TNTECHARC/TALUS-legacy/2015 Stuff/3D Printed Parts - 2015/Shoulders/Left Shoulder/leftPivcenterV1.stl

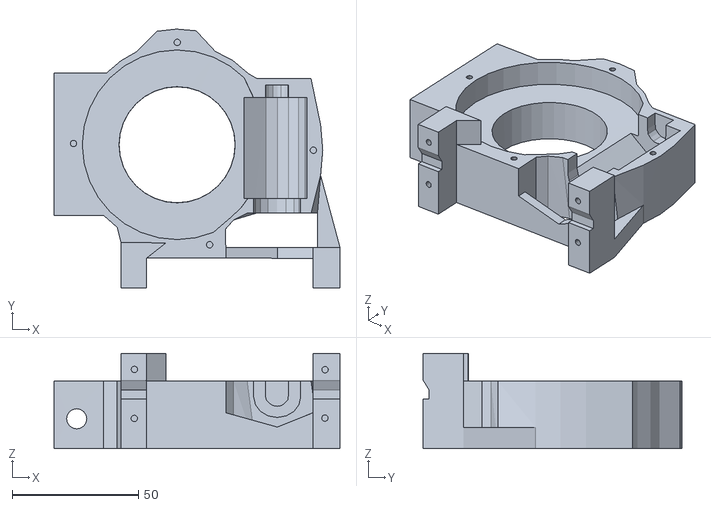
[picture p18: CAD file, 2019-11-21]
2015 Stuff/3D Printed Parts - 2015/Shoulders/Left Shoulder/leftPivcenterV1.stl
113.4 x 102.6 x 37.8
