TNTECHARC/TALUS-legacy/2015 Stuff/3D Printed Parts - 2015/Stomach/StomSupportRightV1.stl

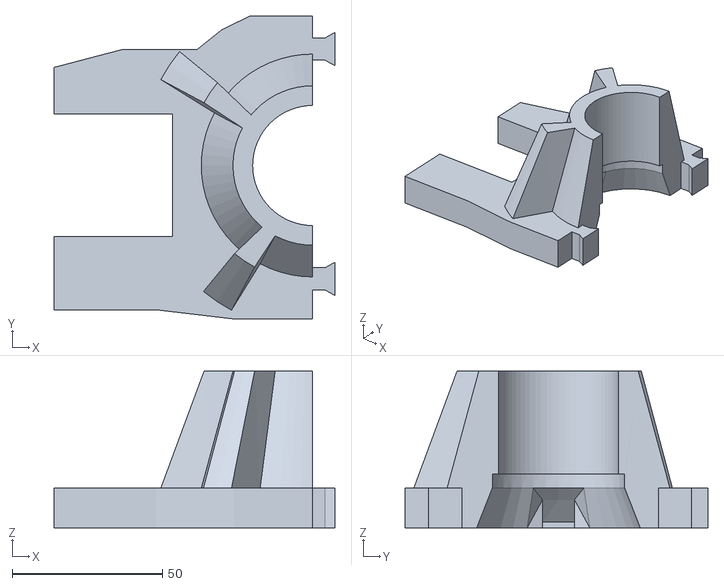
[picture p19: CAD file, 2019-11-21]
2015 Stuff/3D Printed Parts - 2015/Stomach/StomSupportRightV1.stl
93.5 x 101.0 x 52.2
