TNTECHARC/TALUS-legacy/2015 Stuff/F17 ME4140 Animation Project/Matlab Code and Rigid-Body STLS/Right_Forearm.stl

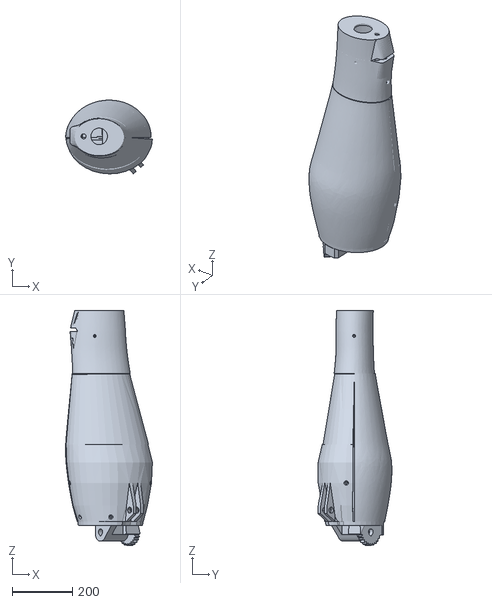
[picture p20: CAD file, 2019-11-21]
2015 Stuff/F17 ME4140 Animation Project/Matlab Code and Rigid-Body STLS/Right_Forearm.stl
287.9 x 244.5 x 779.1
