TNTECHARC/TALUS-legacy/2015 Stuff/3D Printed Parts - 2015/Arms/GearHolderV1.stl

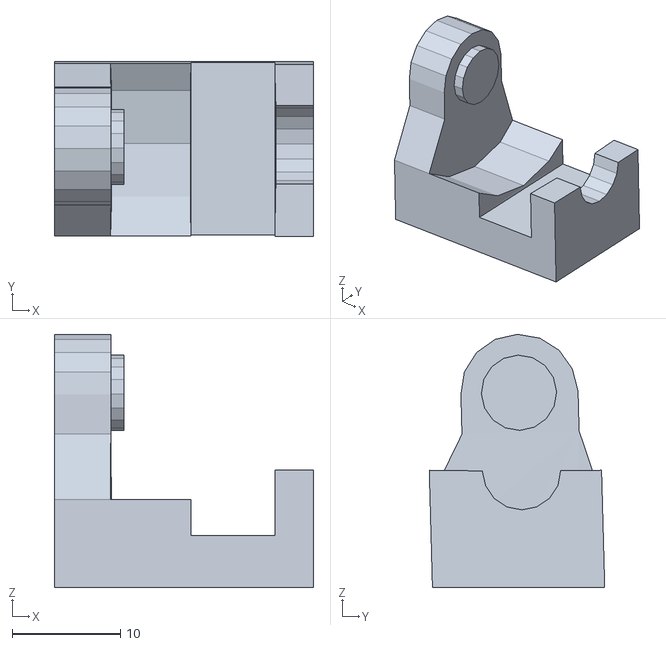
[picture p21: CAD file, 2019-11-21]
2015 Stuff/3D Printed Parts - 2015/Arms/GearHolderV1.stl
23.9 x 16.2 x 23.4
