TNTECHARC/TALUS-legacy/2015 Stuff/3D Printed Parts - 2015/Shoulders/Left Shoulder/PivGearV4.stl

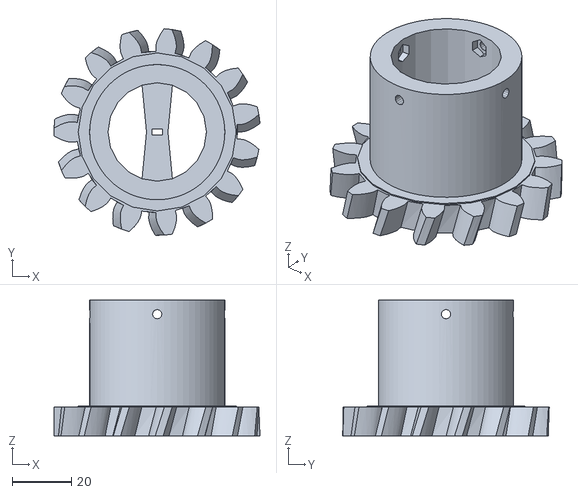
[picture p22: CAD file, 2019-11-21]
2015 Stuff/3D Printed Parts - 2015/Shoulders/Left Shoulder/PivGearV4.stl
69.5 x 69.7 x 45.7
