TNTECHARC/TALUS-legacy/2015 Stuff/3D Printed Parts - 2015/Shoulders/Right Shoulder/PivPotholderV2.stl

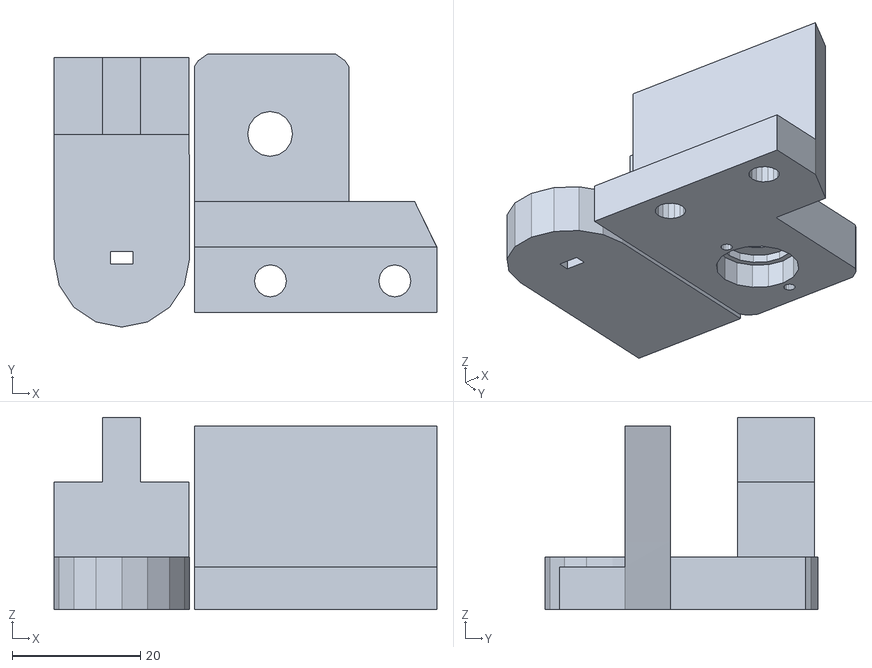
[picture p23: CAD file, 2019-11-21]
2015 Stuff/3D Printed Parts - 2015/Shoulders/Right Shoulder/PivPotholderV2.stl
59.6 x 42.5 x 30.0
