TNTECHARC/TALUS-legacy/2015 Stuff/3D Printed Parts - 2015/Stomach/TStoBackRightV1.stl

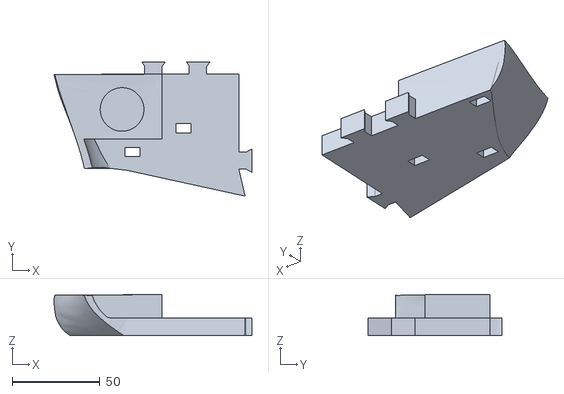
[picture p24: CAD file, 2019-11-21]
2015 Stuff/3D Printed Parts - 2015/Stomach/TStoBackRightV1.stl
112.7 x 76.4 x 23.4
