TNTECHARC/TALUS-legacy/2015 Stuff/3D Printed Parts - 2015/Torso/NeckV1.stl

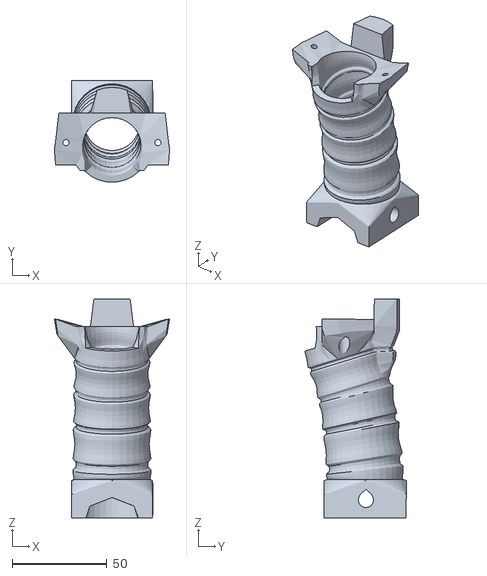
[picture p25: CAD file, 2019-11-21]
2015 Stuff/3D Printed Parts - 2015/Torso/NeckV1.stl
60.7 x 53.5 x 115.4
