TNTECHARC/TALUS-legacy/2015 Stuff/F17 ME4140 Animation Project/Matlab Code and Rigid-Body STLS/Right_Shoulder2.stl

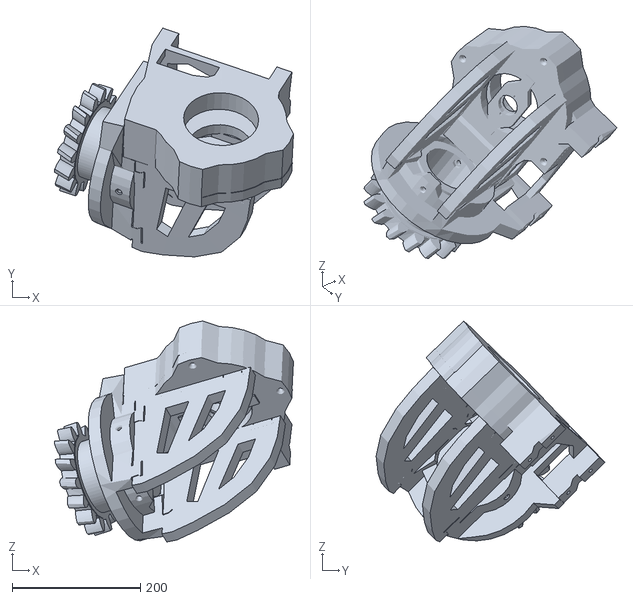
[picture p26: CAD file, 2019-11-21]
2015 Stuff/F17 ME4140 Animation Project/Matlab Code and Rigid-Body STLS/Right_Shoulder2.stl
372.1 x 356.3 x 344.1
