TNTECHARC/TALUS-legacy/2015 Stuff/3D Printed Parts - 2015/Arms/leftRotTitV2.stl

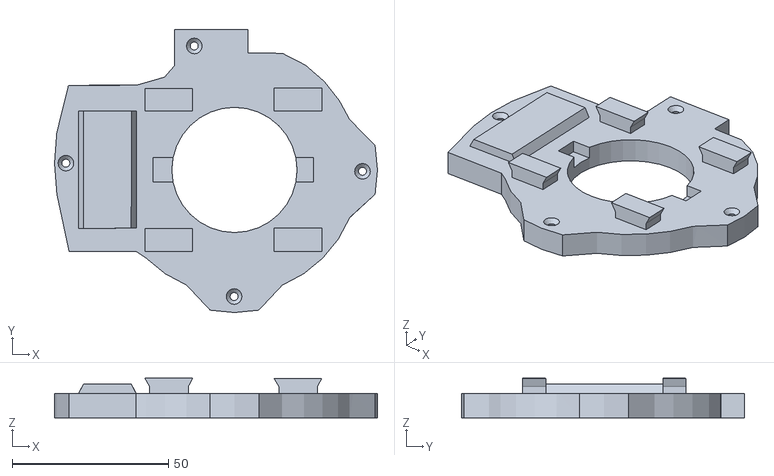
[picture p27: CAD file, 2019-11-21]
2015 Stuff/3D Printed Parts - 2015/Arms/leftRotTitV2.stl
103.5 x 90.7 x 12.7
