TNTECHARC/TALUS-legacy/2015 Stuff/3D Printed Parts - 2015/Shoulders/Left Shoulder/servoholderV1.stl

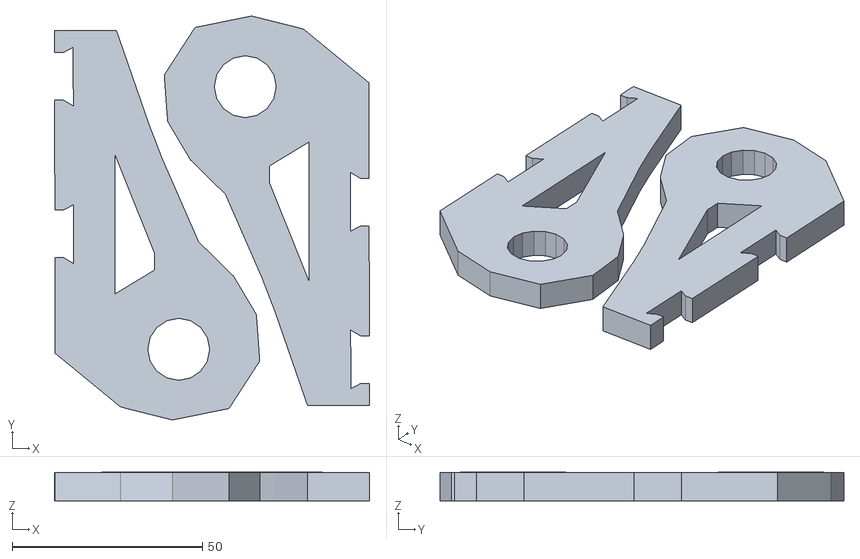
[picture p28: CAD file, 2019-11-21]
2015 Stuff/3D Printed Parts - 2015/Shoulders/Left Shoulder/servoholderV1.stl
82.8 x 106.2 x 7.56
