TNTECHARC/TALUS-legacy/2015 Stuff/3D Printed Parts - 2015/Stomach/TStoFrontLeftV1.stl

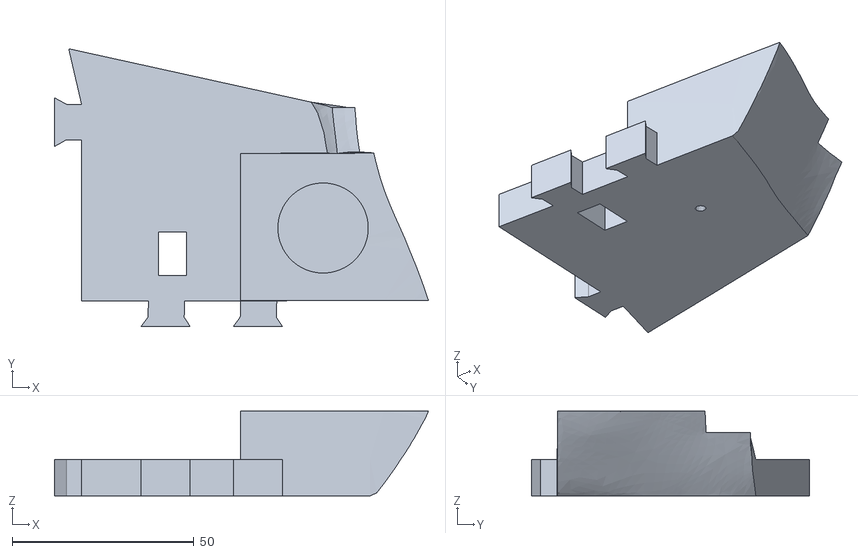
[picture p29: CAD file, 2019-11-21]
2015 Stuff/3D Printed Parts - 2015/Stomach/TStoFrontLeftV1.stl
103.0 x 76.4 x 23.4
