TNTECHARC/TALUS-legacy/2015 Stuff/3D Printed Parts - 2015/Torso/homplateback+V1.stl

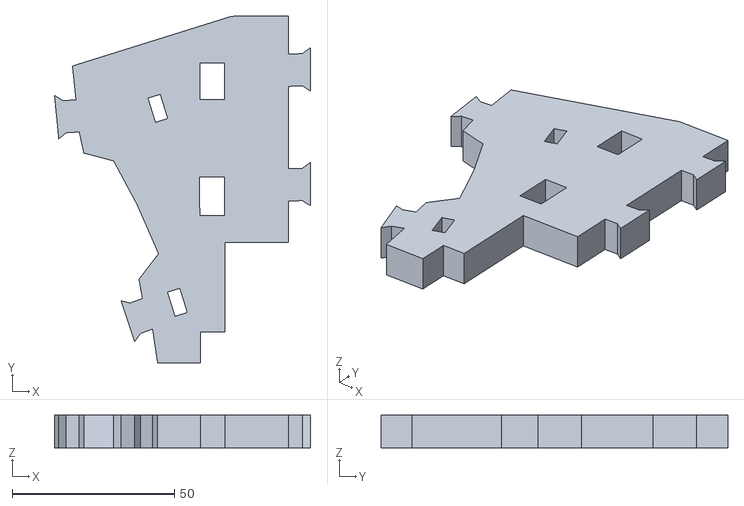
[picture p30: CAD file, 2019-11-21]
2015 Stuff/3D Printed Parts - 2015/Torso/homplateback+V1.stl
79.0 x 107.0 x 10.0
