TNTECHARC/TALUS-legacy/2015 Stuff/3D Printed Parts - 2015/Arms/RotGearV4.stl

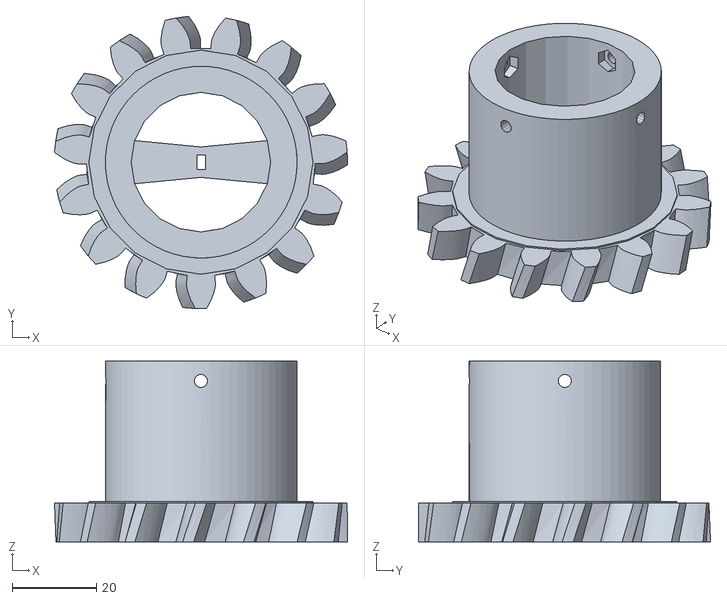
[picture p31: CAD file, 2019-11-21]
2015 Stuff/3D Printed Parts - 2015/Arms/RotGearV4.stl
69.7 x 69.5 x 43.0
