TNTECHARC/TALUS-legacy/2015 Stuff/3D Printed Parts - 2015/Shoulders/Left Shoulder/PivConnectorV1.stl

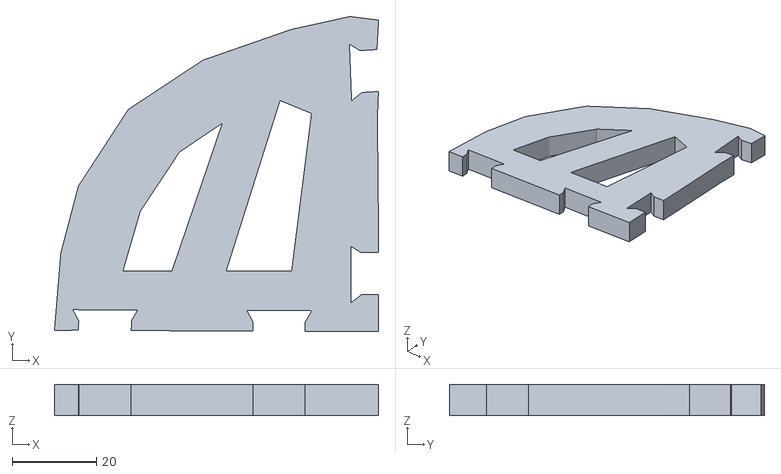
[picture p32: CAD file, 2019-11-21]
2015 Stuff/3D Printed Parts - 2015/Shoulders/Left Shoulder/PivConnectorV1.stl
77.1 x 74.9 x 7.49
