TNTECHARC/TALUS-legacy/2015 Stuff/3D Printed Parts - 2015/Stomach/RollFrontRightV1.stl

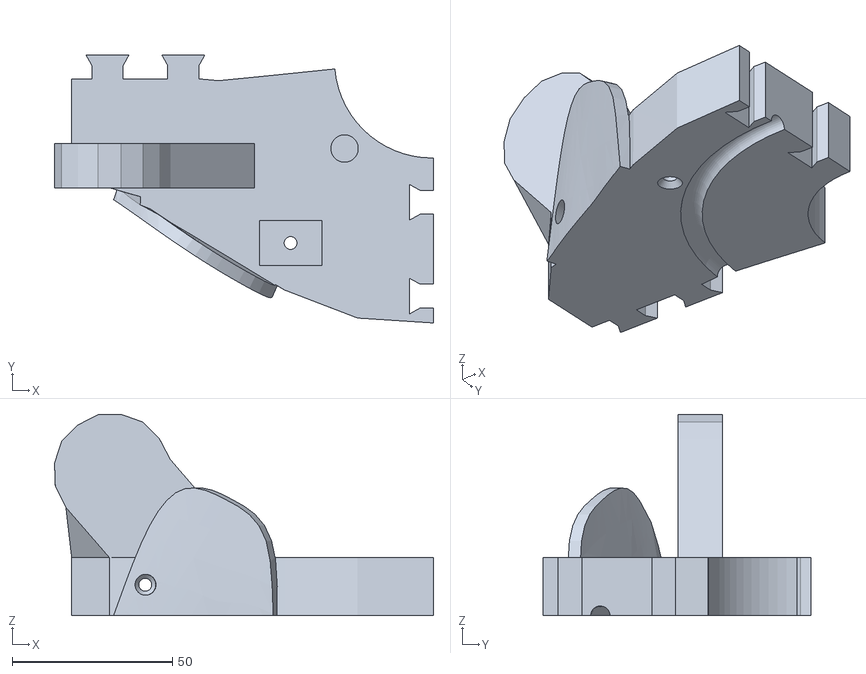
[picture p33: CAD file, 2019-11-21]
2015 Stuff/3D Printed Parts - 2015/Stomach/RollFrontRightV1.stl
118.4 x 83.7 x 62.9
