TNTECHARC/TALUS-legacy/2015 Stuff/3D Printed Parts - 2015/Torso/ThroatHoleV2.stl

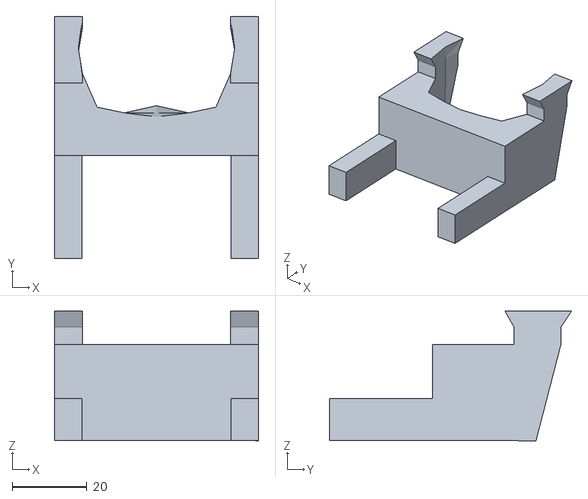
[picture p34: CAD file, 2019-11-21]
2015 Stuff/3D Printed Parts - 2015/Torso/ThroatHoleV2.stl
54.6 x 64.8 x 34.7
