TNTECHARC/TALUS-legacy/2015 Stuff/F17 ME4140 Animation Project/Matlab Code and Rigid-Body STLS/Right_Bicep.stl

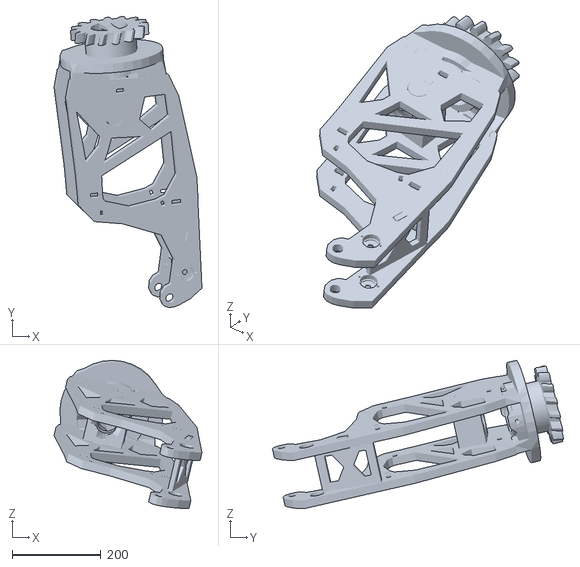
[picture p35: CAD file, 2019-11-21]
2015 Stuff/F17 ME4140 Animation Project/Matlab Code and Rigid-Body STLS/Right_Bicep.stl
334.4 x 657.8 x 335.1
