TNTECHARC/TALUS-legacy/2015 Stuff/3D Printed Parts - 2015/Arms/reinforcerV1.stl

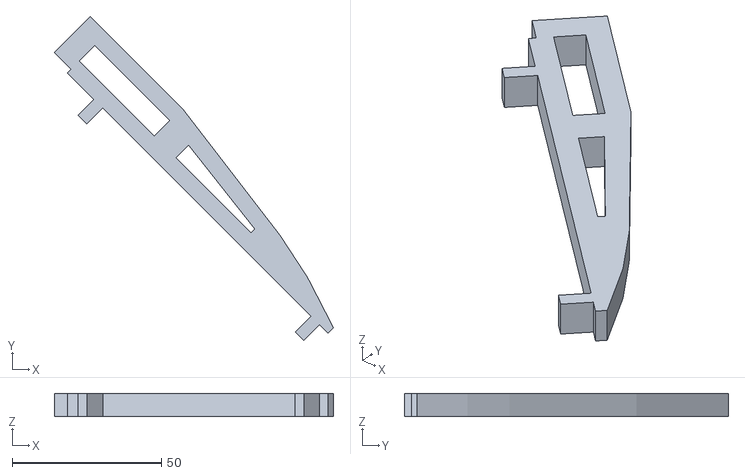
[picture p36: CAD file, 2019-11-21]
2015 Stuff/3D Printed Parts - 2015/Arms/reinforcerV1.stl
93.6 x 108.7 x 7.77
