TNTECHARC/TALUS-legacy/2015 Stuff/3D Printed Parts - 2015/Shoulders/Right Shoulder/PivWormV2.stl

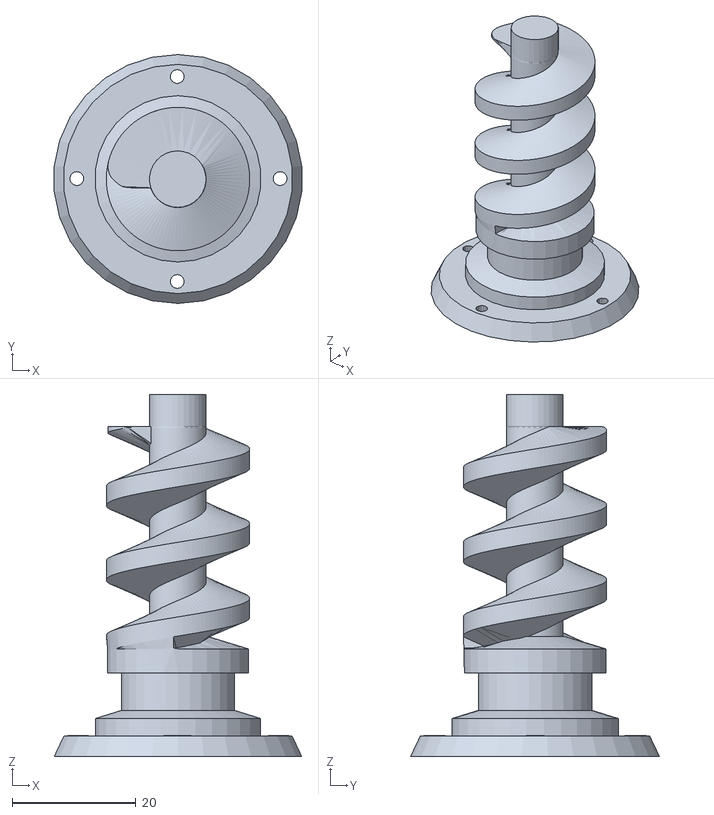
[picture p37: CAD file, 2019-11-21]
2015 Stuff/3D Printed Parts - 2015/Shoulders/Right Shoulder/PivWormV2.stl
39.9 x 40.2 x 58.4
