TNTECHARC/TALUS-legacy/2015 Stuff/3D Printed Parts - 2015/Stomach/TStoPistonRightV2.stl

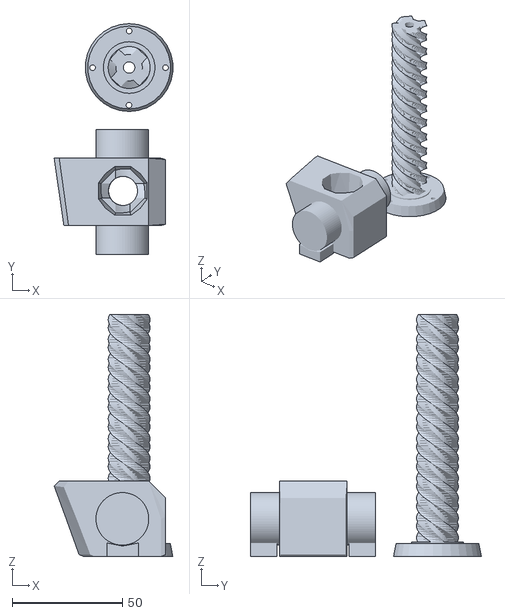
[picture p38: CAD file, 2019-11-21]
2015 Stuff/3D Printed Parts - 2015/Stomach/TStoPistonRightV2.stl
53.8 x 104.6 x 109.7
