TNTECHARC/TALUS-legacy/2015 Stuff/3D Printed Parts - 2015/Torso/KinectSideBackV1 (1).stl

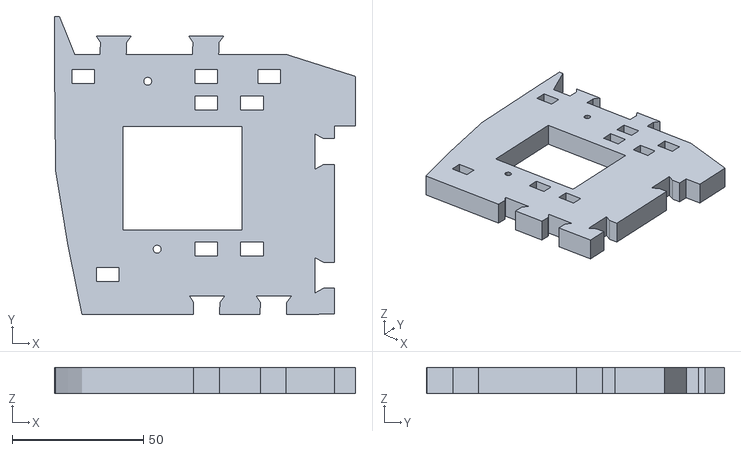
[picture p39: CAD file, 2019-11-21]
2015 Stuff/3D Printed Parts - 2015/Torso/KinectSideBackV1 (1).stl
114.7 x 113.5 x 10.0
