TNTECHARC/TALUS-legacy/2015 Stuff/3D Printed Parts - 2015/Arms/leftRotcenterV2.stl

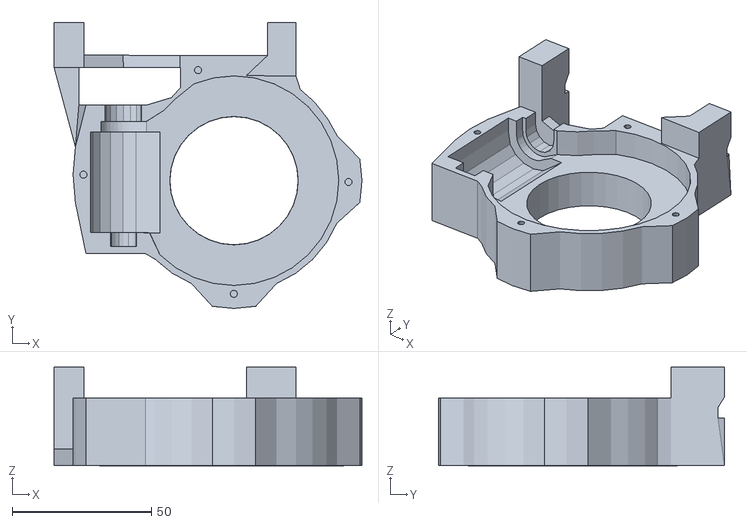
[picture p40: CAD file, 2019-11-21]
2015 Stuff/3D Printed Parts - 2015/Arms/leftRotcenterV2.stl
110.5 x 102.6 x 35.4
