TNTECHARC/TALUS-legacy/2015 Stuff/3D Printed Parts - 2015/Stomach/DiskUnderV1.stl

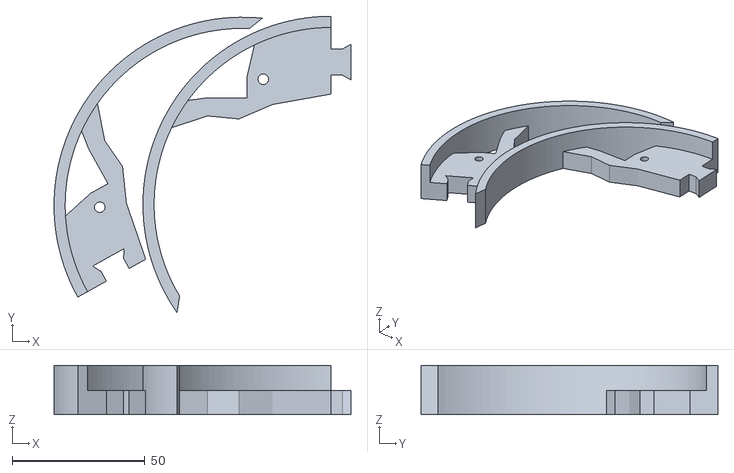
[picture p41: CAD file, 2019-11-21]
2015 Stuff/3D Printed Parts - 2015/Stomach/DiskUnderV1.stl
111.7 x 111.5 x 18.5
