TNTECHARC/TALUS-legacy/2015 Stuff/3D Printed Parts - 2015/Torso/HomLowBack-V1.stl

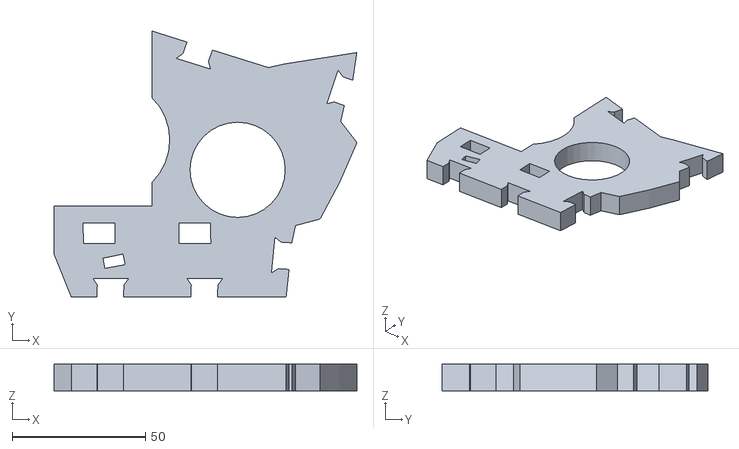
[picture p42: CAD file, 2019-11-21]
2015 Stuff/3D Printed Parts - 2015/Torso/HomLowBack-V1.stl
113.5 x 99.7 x 10.1
