TNTECHARC/TALUS-legacy/2015 Stuff/3D Printed Parts - 2015/Arms/servobaseV1.stl

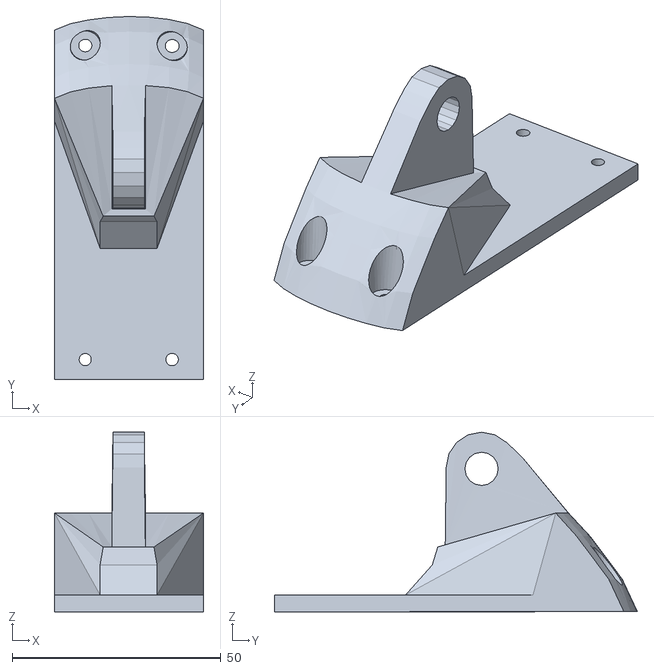
[picture p43: CAD file, 2019-11-21]
2015 Stuff/3D Printed Parts - 2015/Arms/servobaseV1.stl
35.7 x 87.0 x 43.1
