TNTECHARC/TALUS-legacy/2015 Stuff/3D Printed Parts - 2015/Stomach/TStomRotBackV1.stl

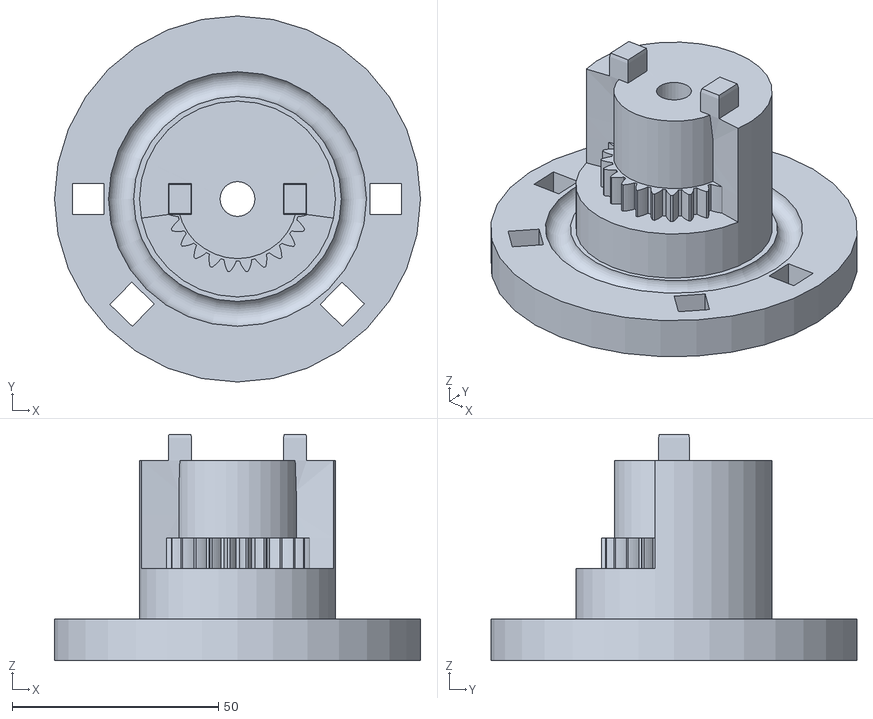
[picture p44: CAD file, 2019-11-21]
2015 Stuff/3D Printed Parts - 2015/Stomach/TStomRotBackV1.stl
88.8 x 88.8 x 54.9
