TNTECHARC/TALUS-legacy/2015 Stuff/F17 ME4140 Animation Project/Matlab Code and Rigid-Body STLS/Right_Shoulder1.stl

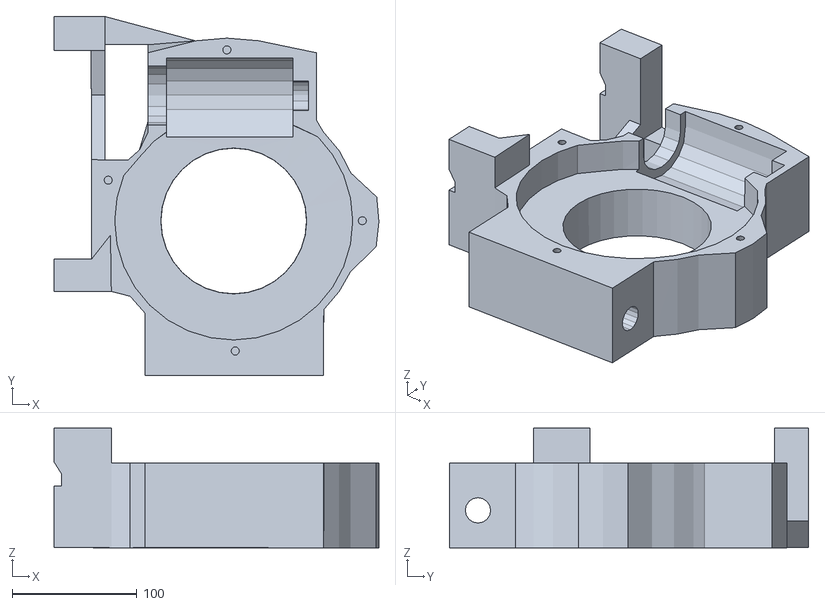
[picture p45: CAD file, 2019-11-21]
2015 Stuff/F17 ME4140 Animation Project/Matlab Code and Rigid-Body STLS/Right_Shoulder1.stl
260.6 x 288.0 x 96.1
