TNTECHARC/TALUS-legacy/2015 Stuff/3D Printed Parts - 2015/Arms/HighArmSideV2.stl

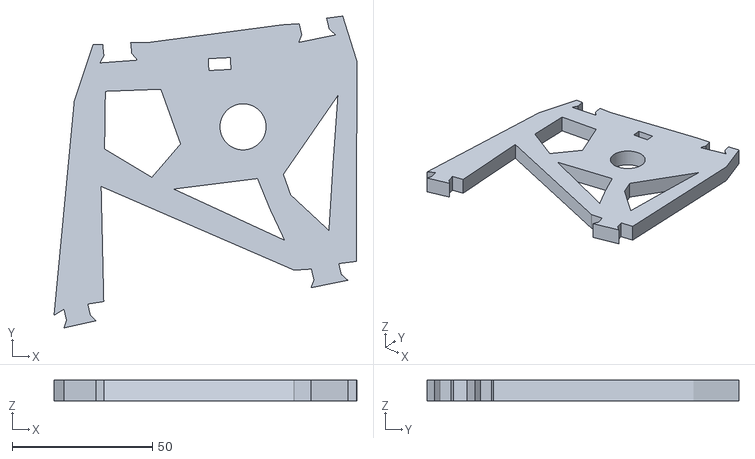
[picture p46: CAD file, 2019-11-21]
2015 Stuff/3D Printed Parts - 2015/Arms/HighArmSideV2.stl
108.0 x 111.2 x 7.49
