TNTECHARC/TALUS-legacy/2015 Stuff/3D Printed Parts - 2015/Shoulders/Left Shoulder/PistonbaseV6.stl

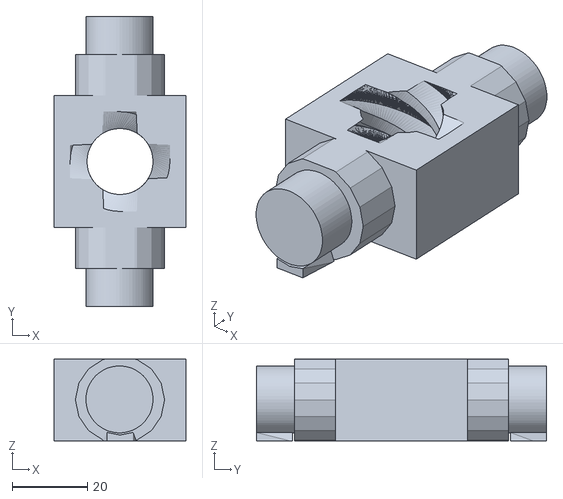
[picture p47: CAD file, 2019-11-21]
2015 Stuff/3D Printed Parts - 2015/Shoulders/Left Shoulder/PistonbaseV6.stl
35.0 x 76.9 x 21.7
