TNTECHARC/TALUS-legacy/2015 Stuff/3D Printed Parts - 2015/Shoulders/Right Shoulder/PivTitV1.stl

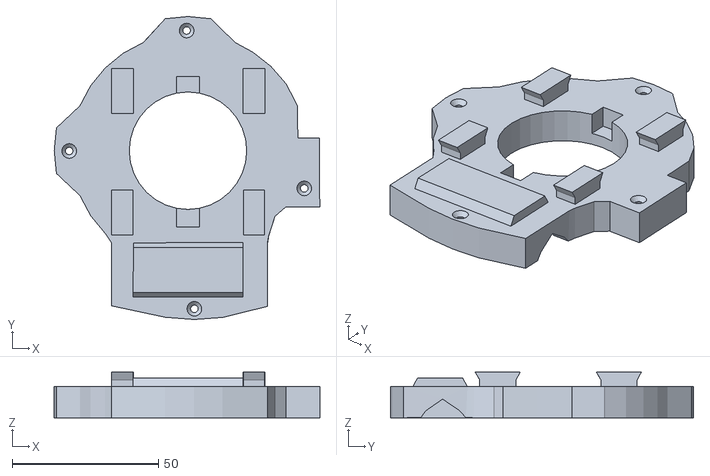
[picture p48: CAD file, 2019-11-21]
2015 Stuff/3D Printed Parts - 2015/Shoulders/Right Shoulder/PivTitV1.stl
90.7 x 103.5 x 15.6
