TNTECHARC/TALUS-legacy/2015 Stuff/3D Printed Parts - 2015/Stomach/TStomCovLeftV2.stl

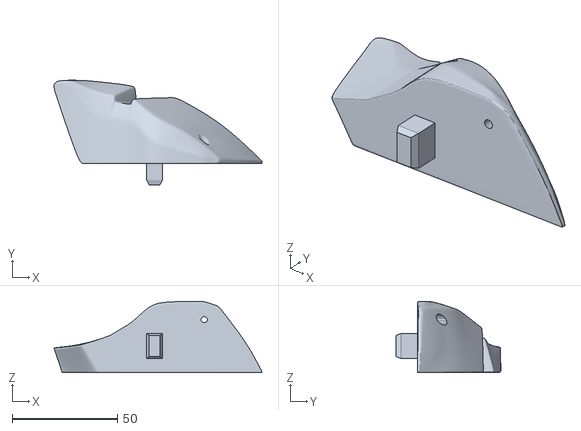
[picture p49: CAD file, 2019-11-21]
2015 Stuff/3D Printed Parts - 2015/Stomach/TStomCovLeftV2.stl
98.9 x 49.7 x 33.8
