TNTECHARC/TALUS-legacy/2015 Stuff/3D Printed Parts - 2015/Torso/InterKinectSideV1.stl

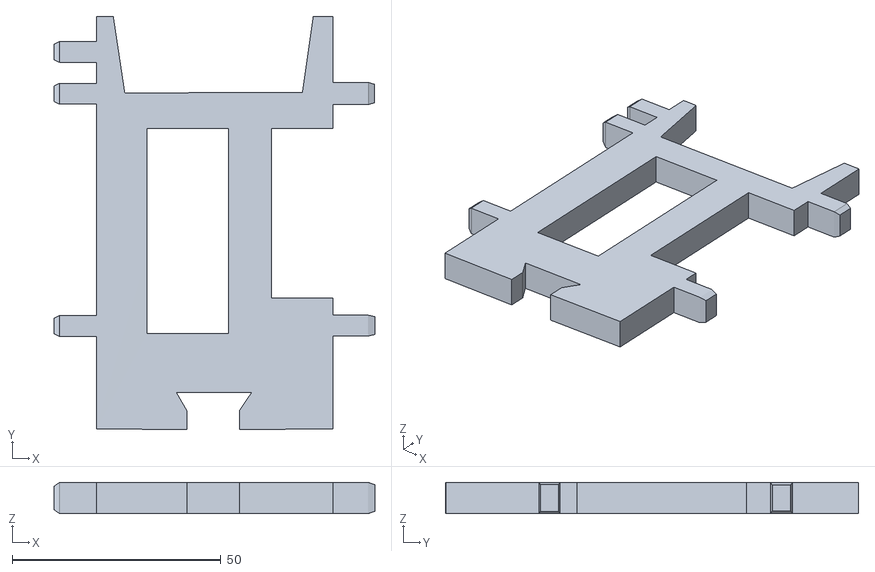
[picture p50: CAD file, 2019-11-21]
2015 Stuff/3D Printed Parts - 2015/Torso/InterKinectSideV1.stl
76.9 x 99.0 x 7.49
