TNTECHARC/TALUS-legacy/2015 Stuff/F17 ME4140 Animation Project/Matlab Code and Rigid-Body STLS/Jaw.stl

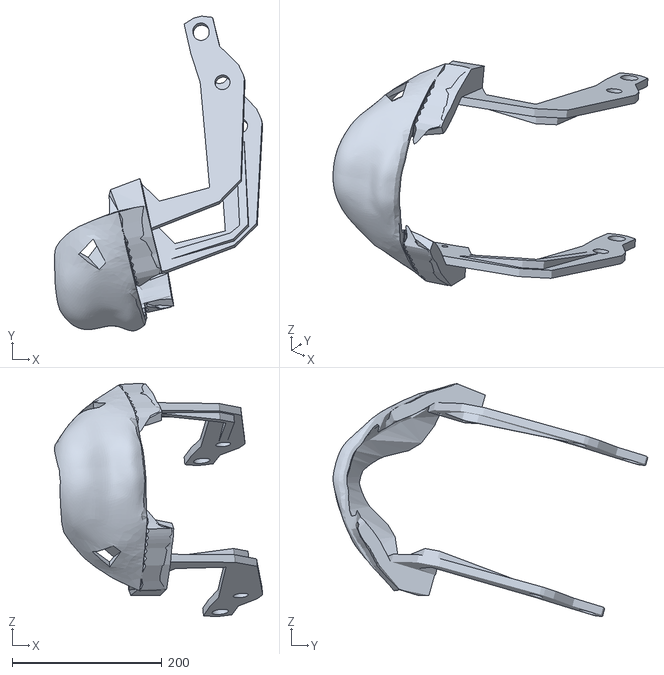
[picture p51: CAD file, 2019-11-21]
2015 Stuff/F17 ME4140 Animation Project/Matlab Code and Rigid-Body STLS/Jaw.stl
278.6 x 420.9 x 311.5
