TNTECHARC/TALUS-legacy/2015 Stuff/3D Printed Parts - 2015/Arms/RotMitV2.stl

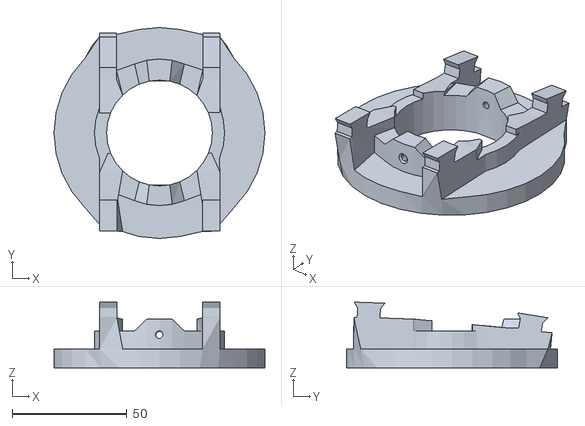
[picture p52: CAD file, 2019-11-21]
2015 Stuff/3D Printed Parts - 2015/Arms/RotMitV2.stl
91.8 x 91.8 x 28.7
