TNTECHARC/TALUS-legacy/2015 Stuff/3D Printed Parts - 2015/Shoulders/Right Shoulder/PivMitV1.stl

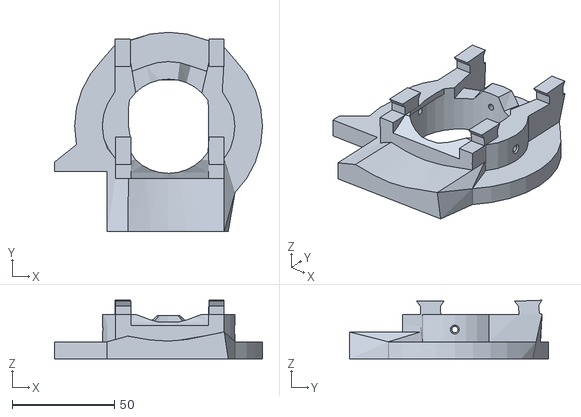
[picture p53: CAD file, 2019-11-21]
2015 Stuff/3D Printed Parts - 2015/Shoulders/Right Shoulder/PivMitV1.stl
101.6 x 97.5 x 28.7
