TNTECHARC/TALUS-legacy/2015 Stuff/3D Printed Parts - 2015/Stomach/RollFrontLeftV1.stl

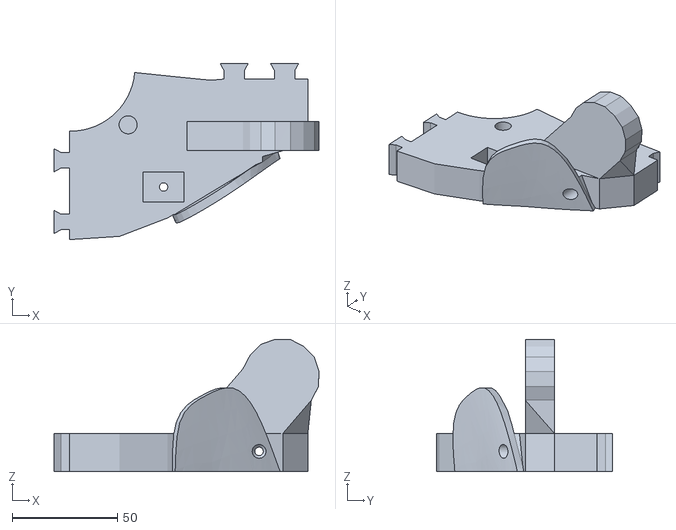
[picture p54: CAD file, 2019-11-21]
2015 Stuff/3D Printed Parts - 2015/Stomach/RollFrontLeftV1.stl
125.9 x 83.7 x 62.9
