TNTECHARC/TALUS-legacy/2015 Stuff/3D Printed Parts - 2015/Torso/homplatebacklow+V1.stl

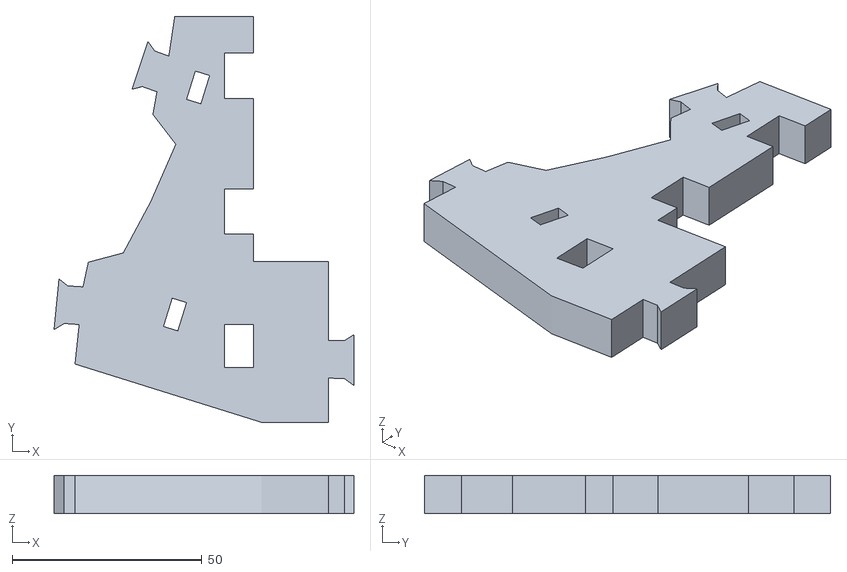
[picture p55: CAD file, 2019-11-21]
2015 Stuff/3D Printed Parts - 2015/Torso/homplatebacklow+V1.stl
79.1 x 107.0 x 10.0
