TNTECHARC/TALUS-legacy/2015 Stuff/3D Printed Parts - 2015/Arms/armtopcover3.stl

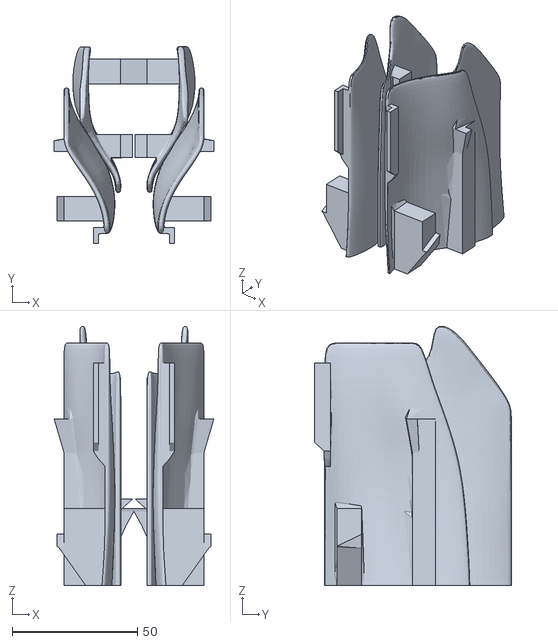
[picture p57: CAD file, 2019-11-21]
2015 Stuff/3D Printed Parts - 2015/Arms/armtopcover3.stl
63.9 x 78.6 x 103.5
