TNTECHARC/TALUS-legacy/2015 Stuff/3D Printed Parts - 2015/Stomach/BotFrontRigtV1.stl

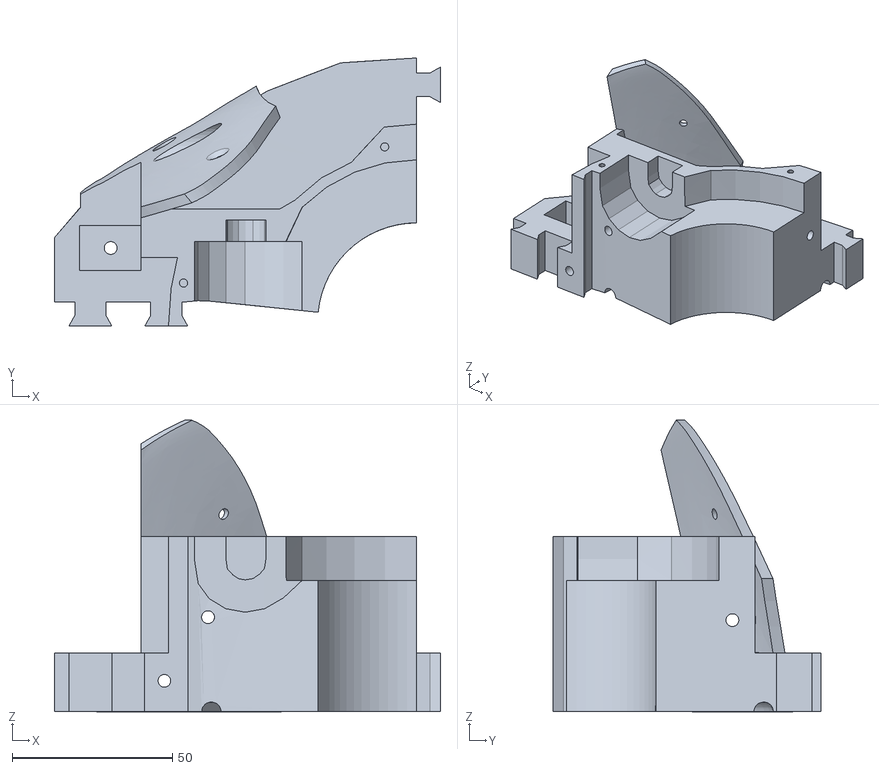
[picture p58: CAD file, 2019-11-21]
2015 Stuff/3D Printed Parts - 2015/Stomach/BotFrontRigtV1.stl
120.5 x 83.7 x 91.0
