TNTECHARC/TALUS-legacy/2015 Stuff/3D Printed Parts - 2015/Arms/PistonbaseantiV2.stl

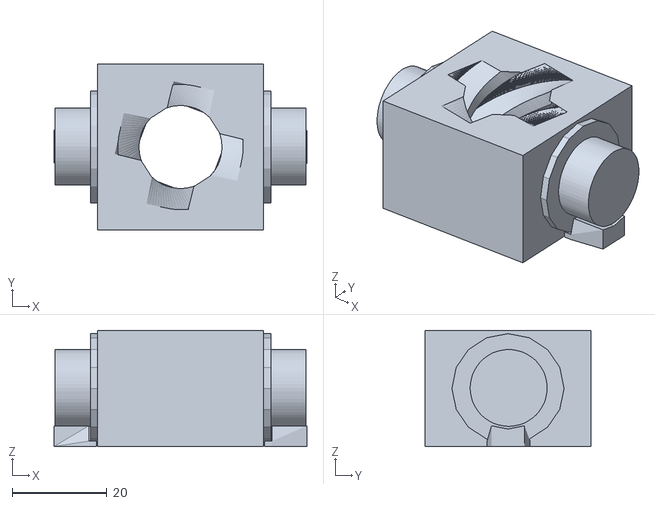
[picture p59: CAD file, 2019-11-21]
2015 Stuff/3D Printed Parts - 2015/Arms/PistonbaseantiV2.stl
53.3 x 35.0 x 24.5
