TNTECHARC/TALUS-legacy/2015 Stuff/3D Printed Parts - 2015/Stomach/TStomRotFrontV1.stl

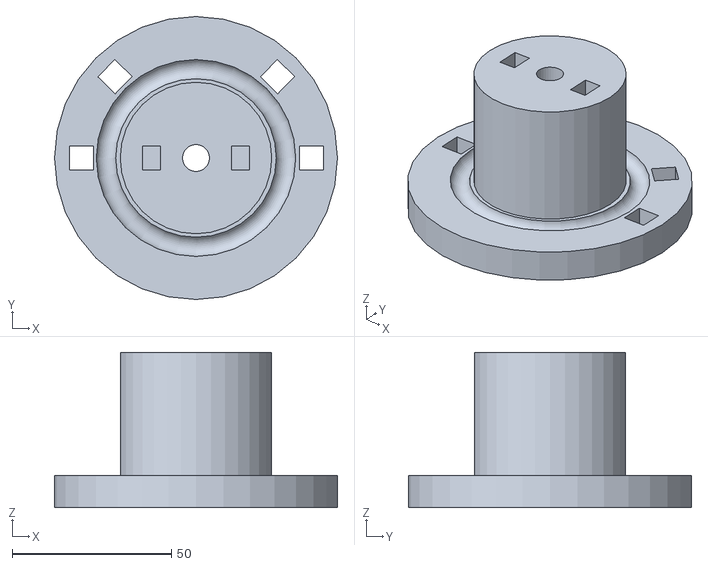
[picture p60: CAD file, 2019-11-21]
2015 Stuff/3D Printed Parts - 2015/Stomach/TStomRotFrontV1.stl
88.8 x 88.8 x 48.6
