TNTECHARC/TALUS-legacy/2015 Stuff/3D Printed Parts - 2015/Torso/ThroatLowerV1.stl

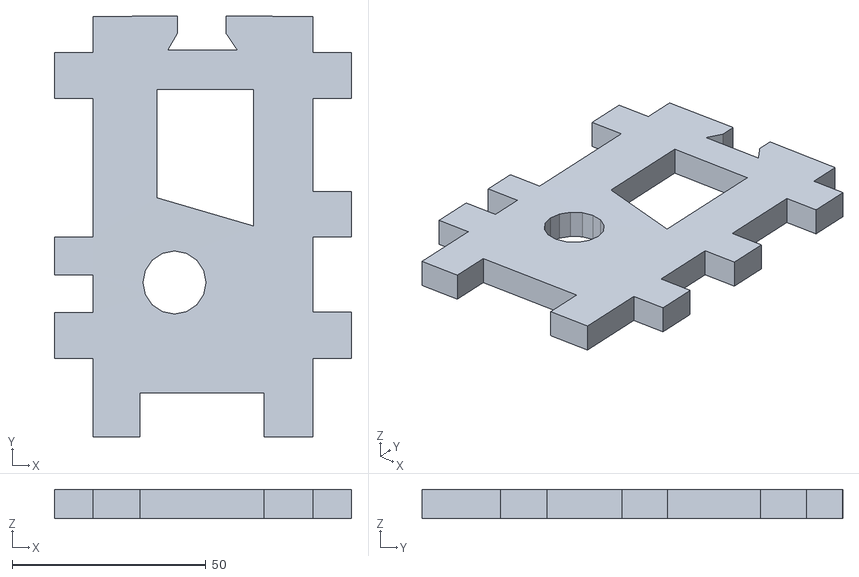
[picture p61: CAD file, 2019-11-21]
2015 Stuff/3D Printed Parts - 2015/Torso/ThroatLowerV1.stl
76.6 x 108.6 x 7.56
