TNTECHARC/TALUS-legacy/2015 Stuff/3D Printed Parts - 2015/Arms/servoholderV1.stl

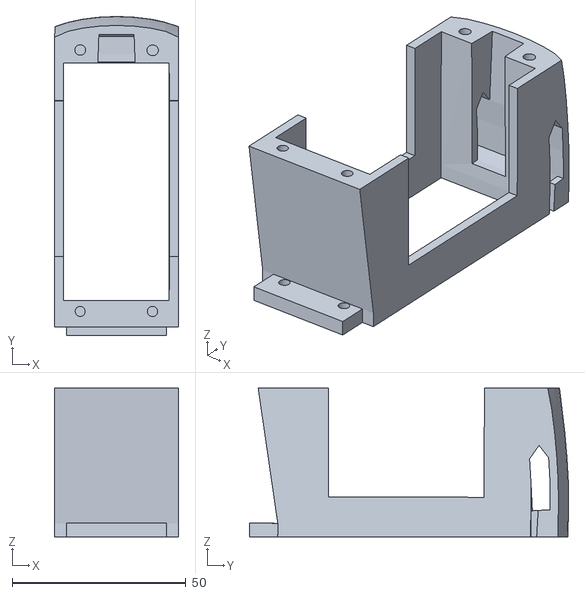
[picture p63: CAD file, 2019-11-21]
2015 Stuff/3D Printed Parts - 2015/Arms/servoholderV1.stl
35.8 x 91.9 x 42.9
