TNTECHARC/TALUS-legacy/2015 Stuff/3D Printed Parts - 2015/Stomach/TStoBackStandLeftV1.stl

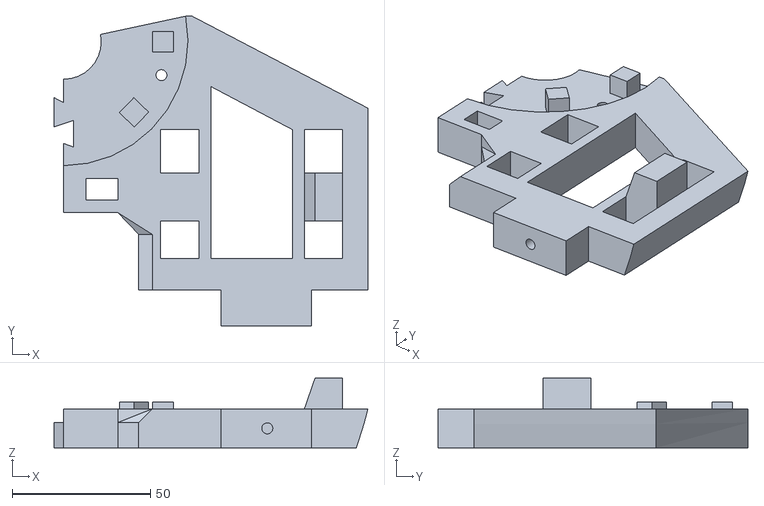
[picture p64: CAD file, 2019-11-21]
2015 Stuff/3D Printed Parts - 2015/Stomach/TStoBackStandLeftV1.stl
113.5 x 111.9 x 25.3
