TNTECHARC/TALUS-legacy/2015 Stuff/3D Printed Parts - 2015/Torso/SternumV1.stl

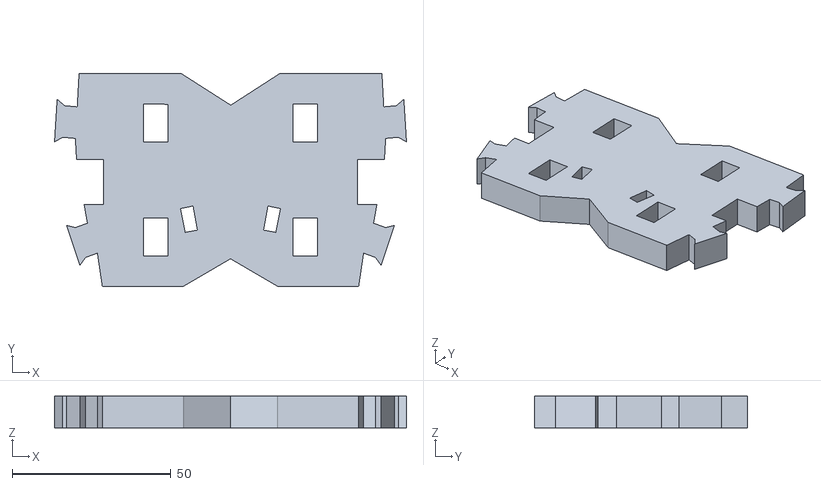
[picture p65: CAD file, 2019-11-21]
2015 Stuff/3D Printed Parts - 2015/Torso/SternumV1.stl
110.9 x 67.0 x 10.0
