TNTECHARC/TALUS-legacy/2015 Stuff/3D Printed Parts - 2015/Arms/armtopcover2.stl

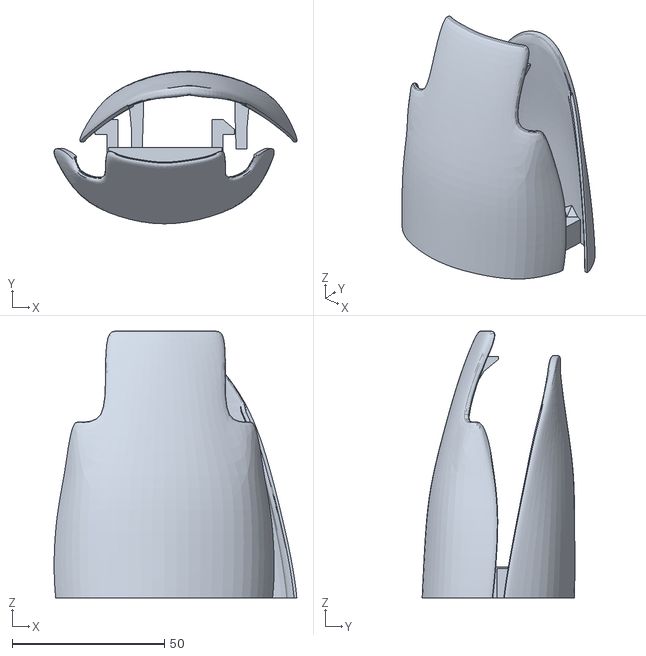
[picture p66: CAD file, 2019-11-21]
2015 Stuff/3D Printed Parts - 2015/Arms/armtopcover2.stl
79.7 x 50.2 x 87.7
