TNTECHARC/TALUS-legacy/2015 Stuff/3D Printed Parts - 2015/Stomach/DiskExternV2.stl

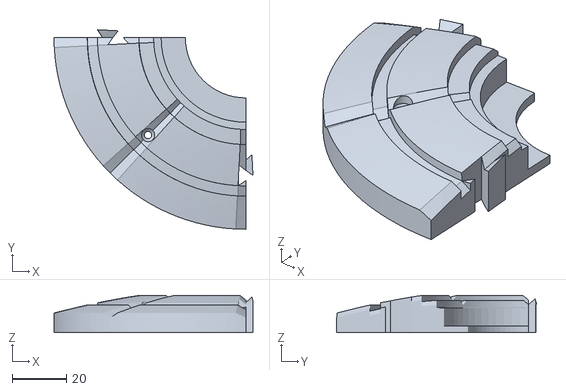
[picture p67: CAD file, 2019-11-21]
2015 Stuff/3D Printed Parts - 2015/Stomach/DiskExternV2.stl
73.5 x 73.7 x 13.7
