TNTECHARC/TALUS-legacy/2015 Stuff/3D Printed Parts - 2015/Torso/KinectMidBackV1 (1).stl

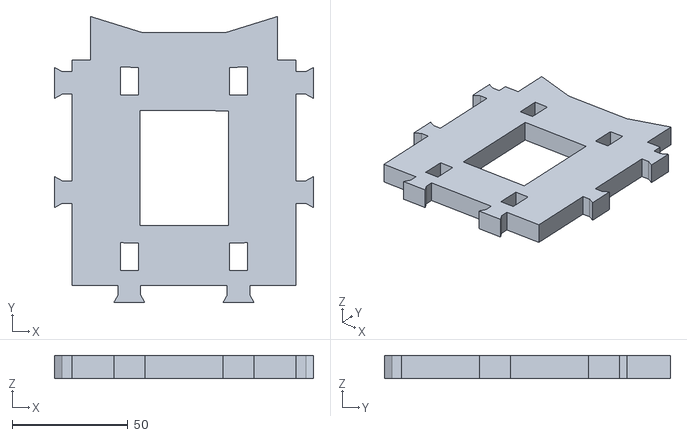
[picture p68: CAD file, 2019-11-21]
2015 Stuff/3D Printed Parts - 2015/Torso/KinectMidBackV1 (1).stl
111.7 x 123.4 x 10.0
