TNTECHARC/TALUS-legacy/2015 Stuff/3D Printed Parts - 2015/Stomach/MidWormRightV1.stl

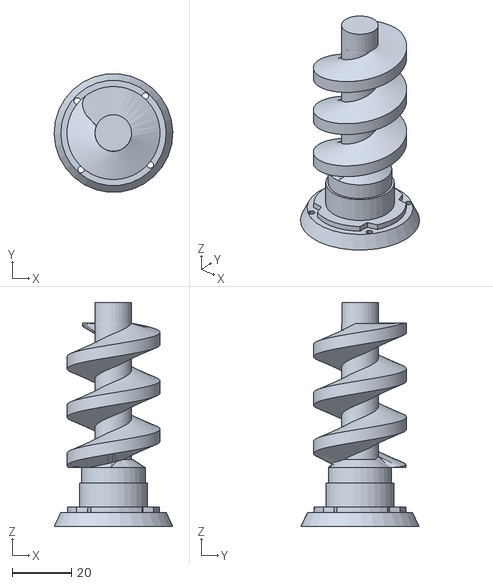
[picture p69: CAD file, 2019-11-21]
2015 Stuff/3D Printed Parts - 2015/Stomach/MidWormRightV1.stl
40.1 x 39.9 x 75.6
