TNTECHARC/TALUS-legacy/2015 Stuff/3D Printed Parts - 2015/Torso/ThroatHolderV1.stl

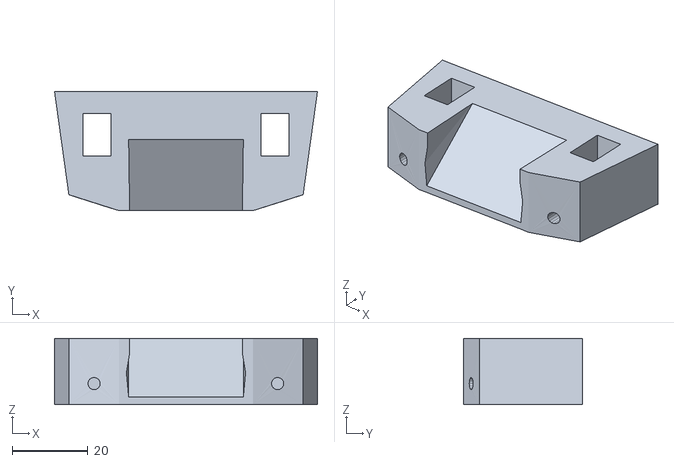
[picture p70: CAD file, 2019-11-21]
2015 Stuff/3D Printed Parts - 2015/Torso/ThroatHolderV1.stl
69.4 x 31.5 x 17.5
