TNTECHARC/TALUS-legacy/2015 Stuff/3D Printed Parts - 2015/Arms/spacerV1.stl

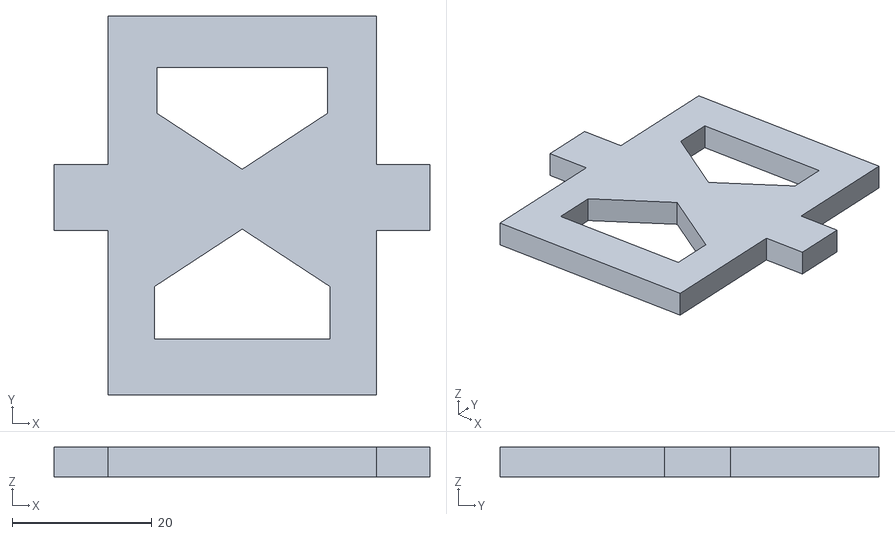
[picture p71: CAD file, 2019-11-21]
2015 Stuff/3D Printed Parts - 2015/Arms/spacerV1.stl
53.8 x 54.3 x 4.23
