TNTECHARC/TALUS-legacy/2015 Stuff/3D Printed Parts - 2015/Stomach/TStomSpacerV1.stl

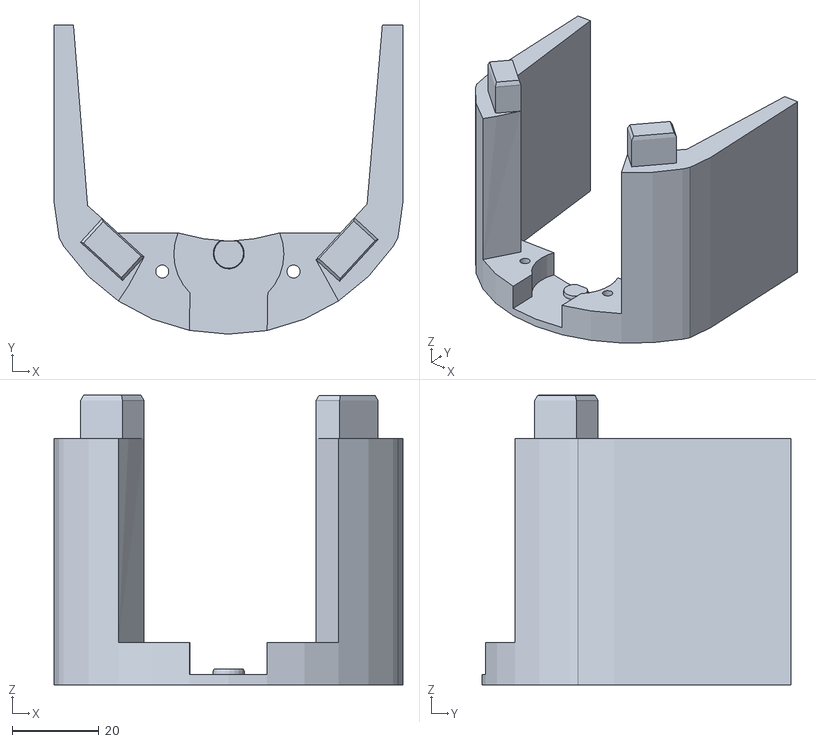
[picture p72: CAD file, 2019-11-21]
2015 Stuff/3D Printed Parts - 2015/Stomach/TStomSpacerV1.stl
80.5 x 71.3 x 66.8
