TNTECHARC/TALUS-legacy/2015 Stuff/3D Printed Parts - 2015/Torso/InterKinectMidV1.stl

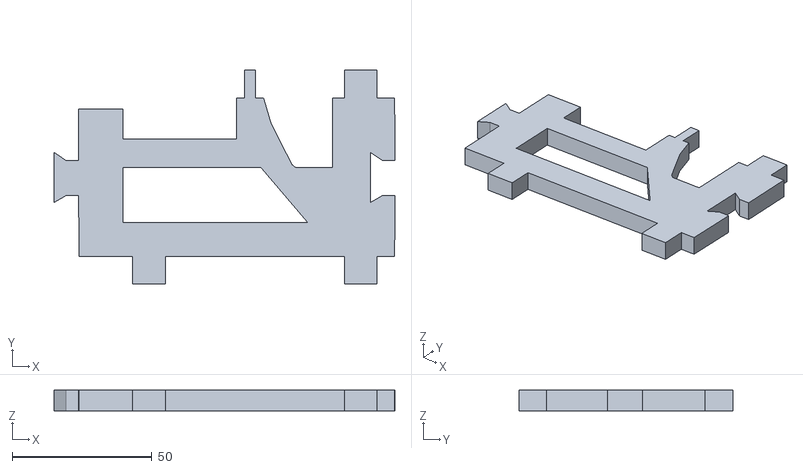
[picture p73: CAD file, 2019-11-21]
2015 Stuff/3D Printed Parts - 2015/Torso/InterKinectMidV1.stl
122.0 x 76.7 x 7.49
