TNTECHARC/TALUS-legacy/2015 Stuff/3D Printed Parts - 2015/Arms/armtopcover1.stl

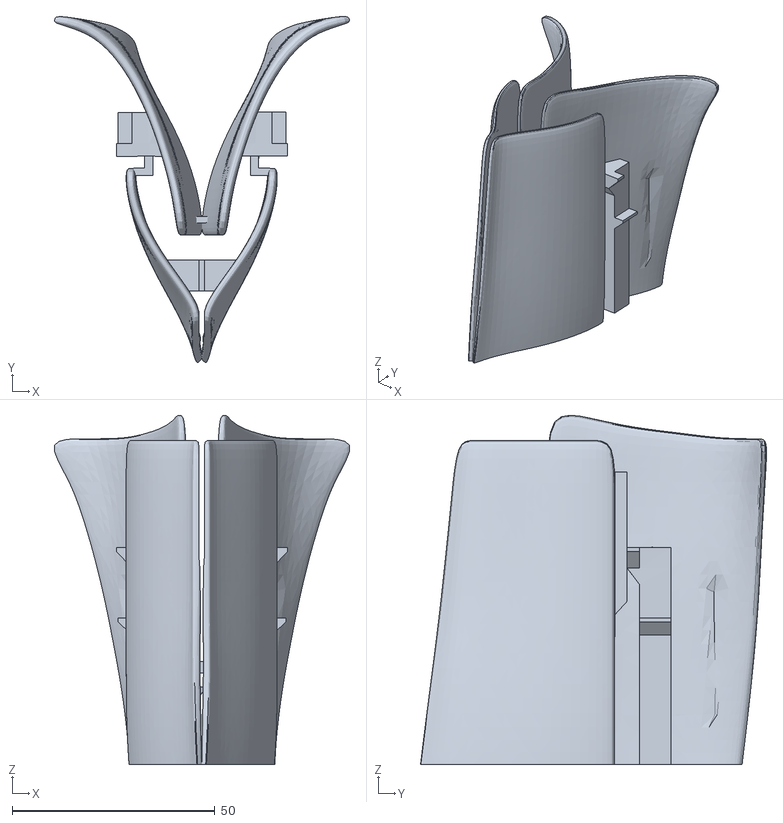
[picture p74: CAD file, 2019-11-21]
2015 Stuff/3D Printed Parts - 2015/Arms/armtopcover1.stl
72.7 x 85.2 x 86.1
