TNTECHARC/TALUS-legacy/2015 Stuff/3D Printed Parts - 2015/Stomach/MidPotHolderV1.stl

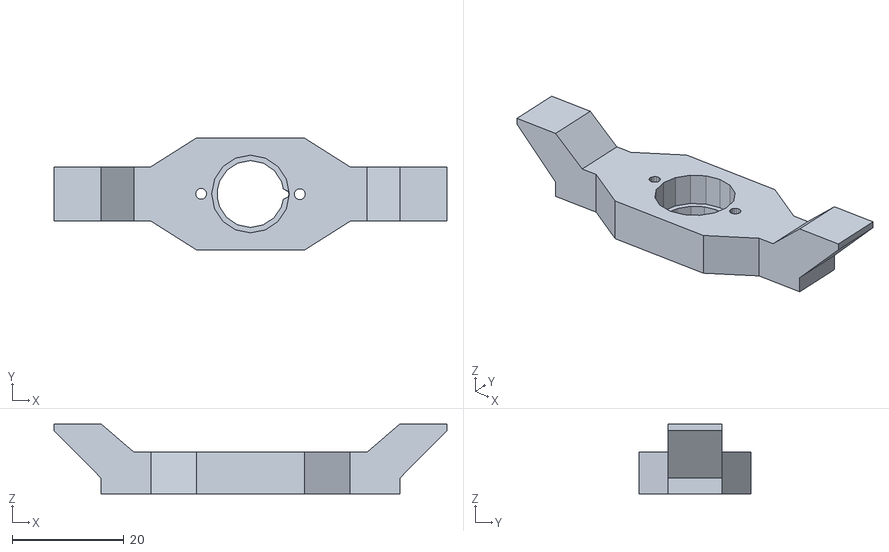
[picture p75: CAD file, 2019-11-21]
2015 Stuff/3D Printed Parts - 2015/Stomach/MidPotHolderV1.stl
70.3 x 20.1 x 12.5
