TNTECHARC/TALUS-legacy/2015 Stuff/3D Printed Parts - 2015/Arms/gearpotentioV1.stl

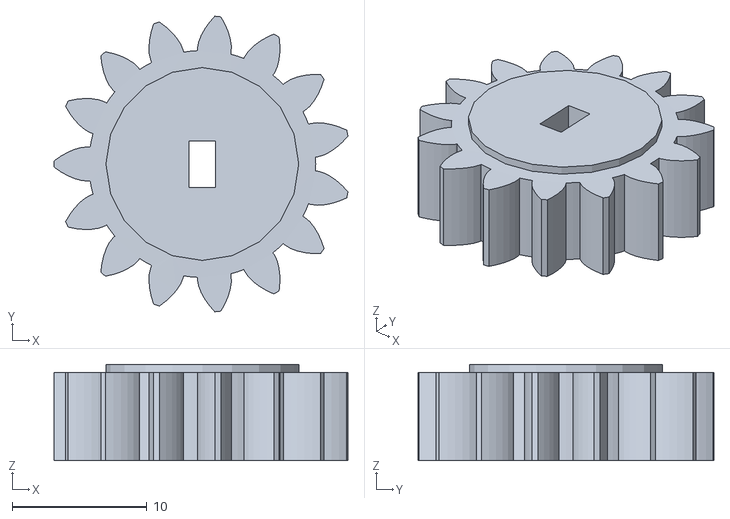
[picture p77: CAD file, 2019-11-21]
2015 Stuff/3D Printed Parts - 2015/Arms/gearpotentioV1.stl
21.8 x 22.0 x 7.15
