TNTECHARC/TALUS-legacy/2015 Stuff/3D Printed Parts - 2015/Arms/lowarmsideV1.stl

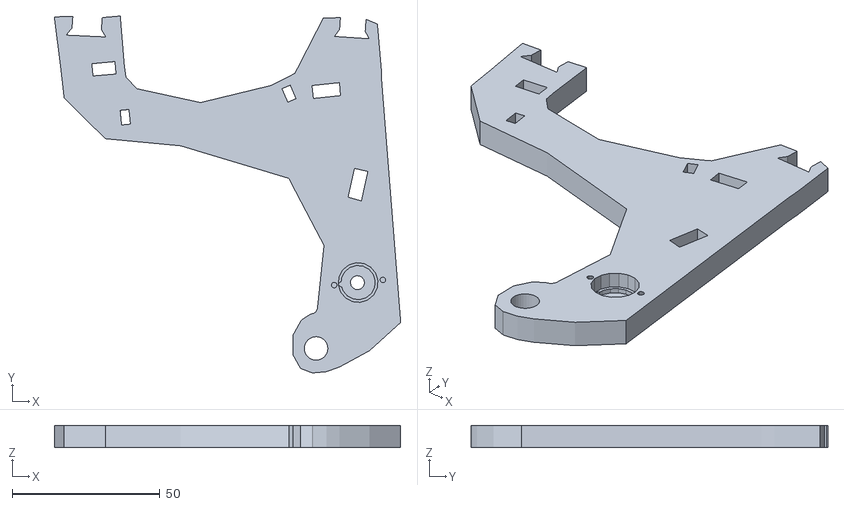
[picture p78: CAD file, 2019-11-21]
2015 Stuff/3D Printed Parts - 2015/Arms/lowarmsideV1.stl
117.3 x 120.9 x 7.50
