TNTECHARC/TALUS-legacy/2015 Stuff/3D Printed Parts - 2015/Stomach/StomSupportLeftV1.stl

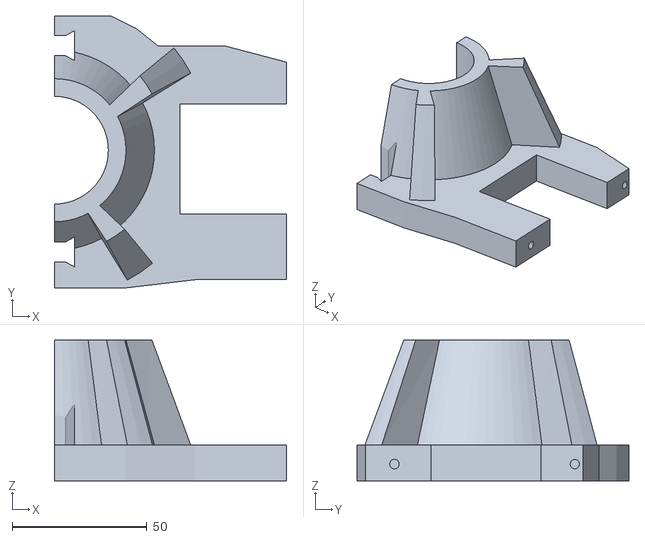
[picture p79: CAD file, 2019-11-21]
2015 Stuff/3D Printed Parts - 2015/Stomach/StomSupportLeftV1.stl
86.2 x 101.0 x 52.2
