TNTECHARC/TALUS-legacy/2015 Stuff/3D Printed Parts - 2015/Arms/RotWormV5.stl

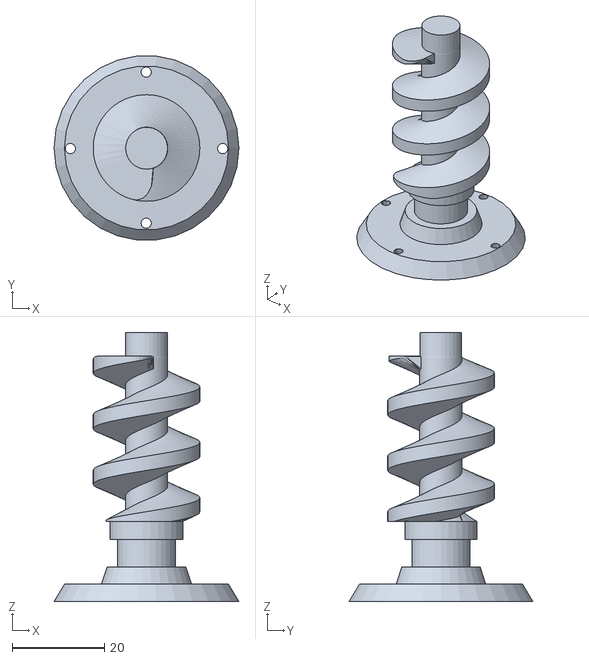
[picture p80: CAD file, 2019-11-21]
2015 Stuff/3D Printed Parts - 2015/Arms/RotWormV5.stl
40.2 x 39.9 x 58.4
