TNTECHARC/TALUS-legacy/2015 Stuff/3D Printed Parts - 2015/Stomach/TStoFrontStandV2.stl

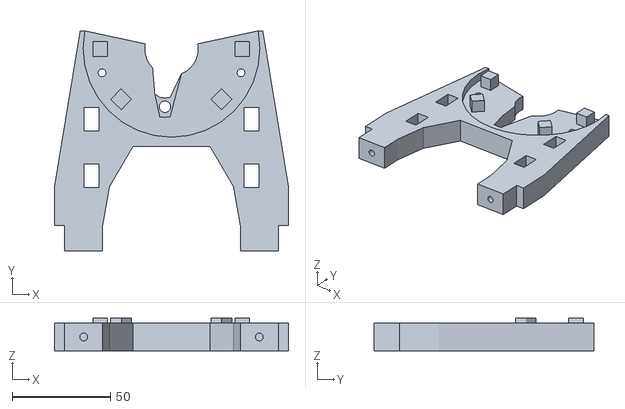
[picture p81: CAD file, 2019-11-21]
2015 Stuff/3D Printed Parts - 2015/Stomach/TStoFrontStandV2.stl
118.9 x 111.9 x 16.7
