TNTECHARC/TALUS-legacy/2015 Stuff/3D Printed Parts - 2015/Stomach/ServoBackV1.stl

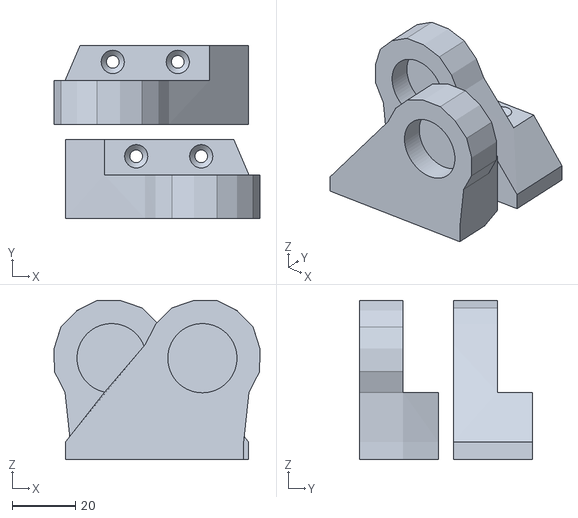
[picture p82: CAD file, 2019-11-21]
2015 Stuff/3D Printed Parts - 2015/Stomach/ServoBackV1.stl
65.1 x 54.8 x 50.3
