TNTECHARC/TALUS-legacy/2015 Stuff/3D Printed Parts - 2015/Stomach/TStomPotHolderv1.stl

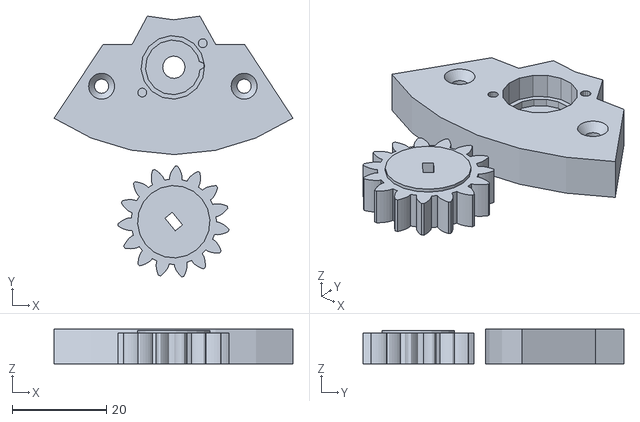
[picture p83: CAD file, 2019-11-21]
2015 Stuff/3D Printed Parts - 2015/Stomach/TStomPotHolderv1.stl
50.7 x 55.4 x 7.42
