TNTECHARC/TALUS-legacy/2015 Stuff/3D Printed Parts - 2015/Stomach/BotCapRightV1.stl

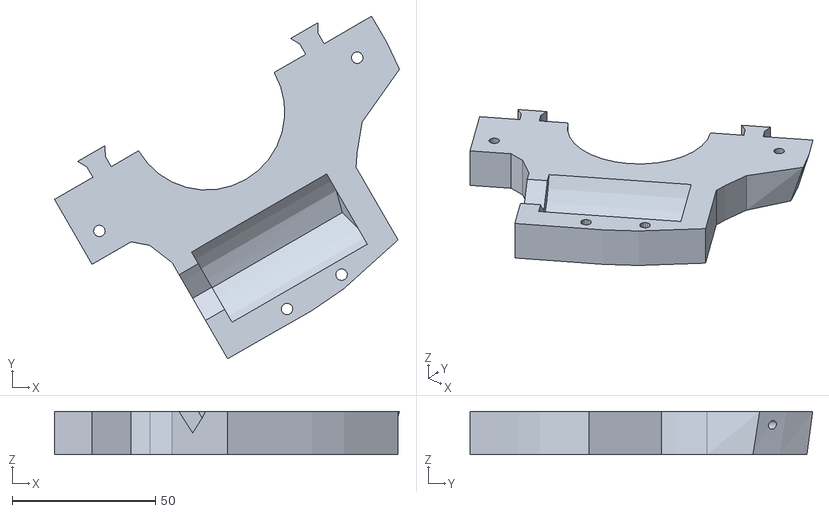
[picture p84: CAD file, 2019-11-21]
2015 Stuff/3D Printed Parts - 2015/Stomach/BotCapRightV1.stl
120.3 x 119.4 x 15.1
