TNTECHARC/TALUS-legacy/2015 Stuff/3D Printed Parts - 2015/Stomach/TStoServoHolsterV2.stl

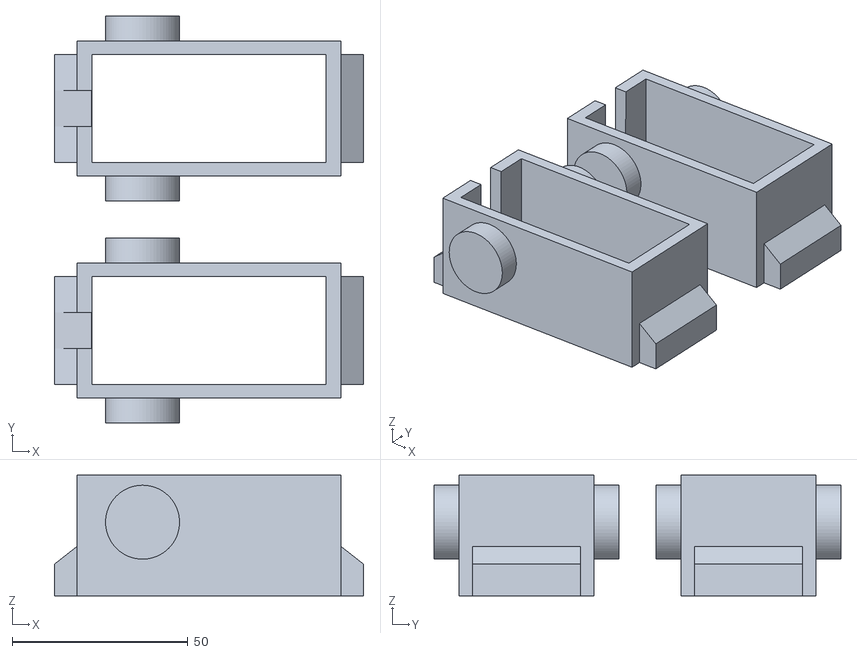
[picture p85: CAD file, 2019-11-21]
2015 Stuff/3D Printed Parts - 2015/Stomach/TStoServoHolsterV2.stl
87.9 x 115.8 x 34.4
