TNTECHARC/TALUS-legacy/2015 Stuff/3D Printed Parts - 2015/Stomach/TStoMiddleV1.stl

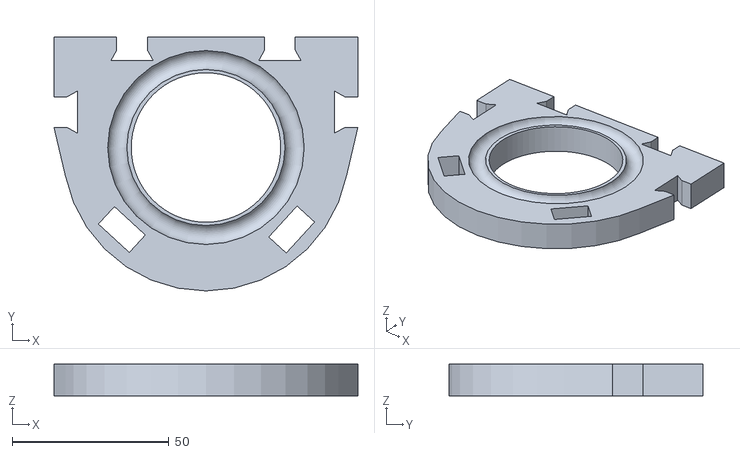
[picture p86: CAD file, 2019-11-21]
2015 Stuff/3D Printed Parts - 2015/Stomach/TStoMiddleV1.stl
96.8 x 80.9 x 10.1
