TNTECHARC/TALUS-legacy/2015 Stuff/3D Printed Parts - 2015/Stomach/StomGearV2.stl

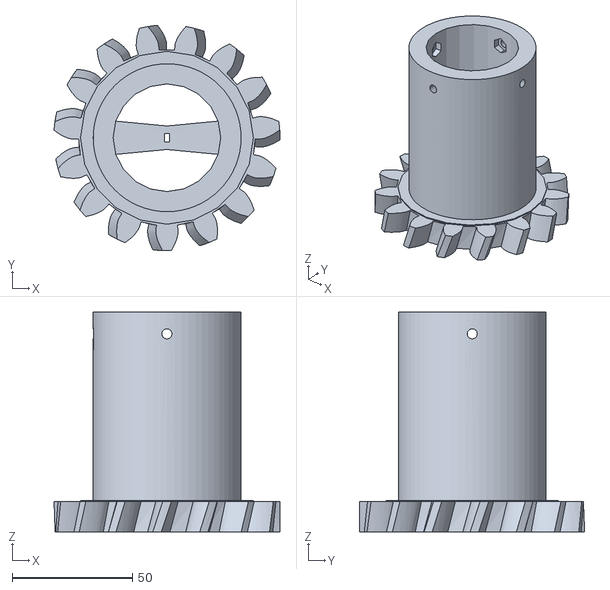
[picture p87: CAD file, 2019-11-21]
2015 Stuff/3D Printed Parts - 2015/Stomach/StomGearV2.stl
94.0 x 93.8 x 91.4
