TNTECHARC/TALUS-legacy/2015 Stuff/3D Printed Parts - 2015/Stomach/RollBackLeftV1.stl

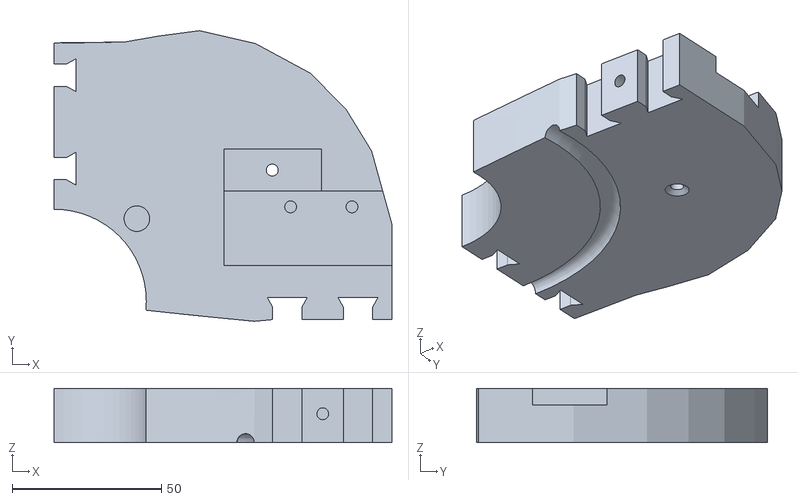
[picture p88: CAD file, 2019-11-21]
2015 Stuff/3D Printed Parts - 2015/Stomach/RollBackLeftV1.stl
113.2 x 97.3 x 18.2
