TNTECHARC/TALUS-legacy/2015 Stuff/3D Printed Parts - 2015/Stomach/DiskInternV3 .stl

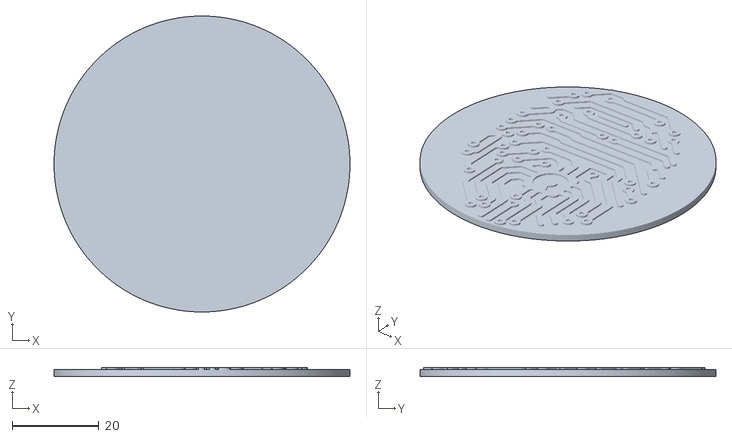
[picture p89: CAD file, 2019-11-21]
2015 Stuff/3D Printed Parts - 2015/Stomach/DiskInternV3 .stl
68.1 x 68.1 x 2.05
