TNTECHARC/TALUS-legacy/2015 Stuff/3D Printed Parts - 2015/Stomach/BotFrontLeftV1.stl

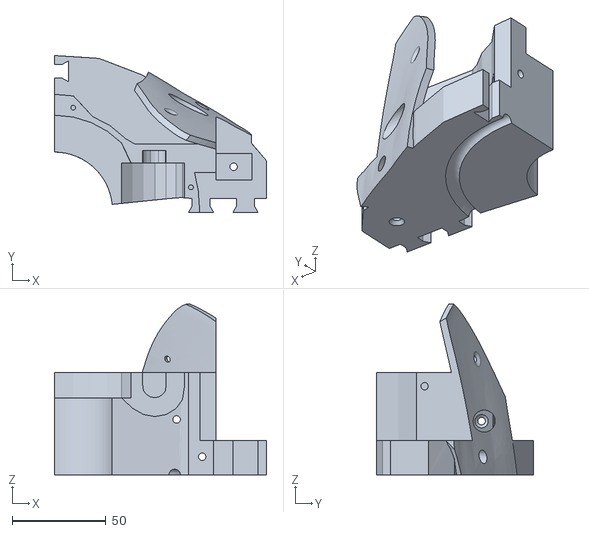
[picture p90: CAD file, 2019-11-21]
2015 Stuff/3D Printed Parts - 2015/Stomach/BotFrontLeftV1.stl
113.0 x 83.7 x 91.0
