TNTECHARC/TALUS-legacy/2015 Stuff/3D Printed Parts - 2015/Stomach/BotBackLeftV1.stl

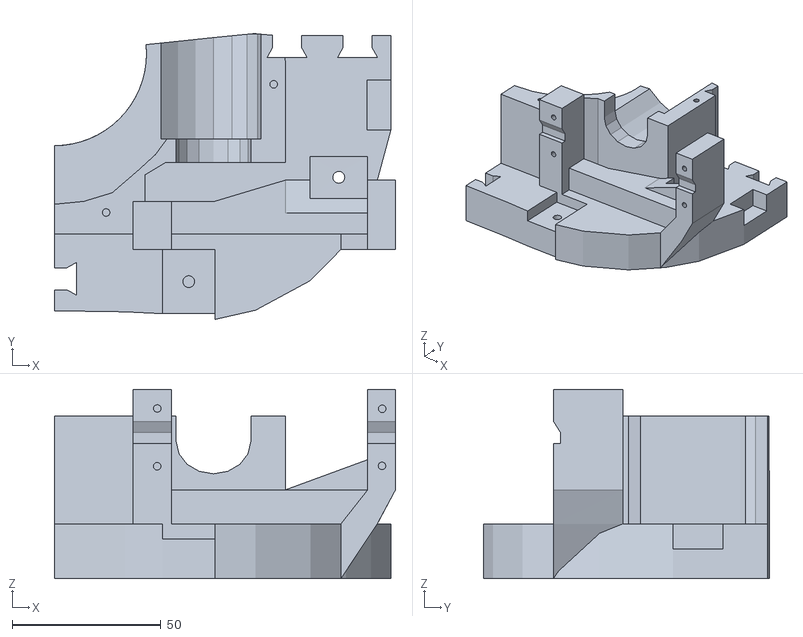
[picture p91: CAD file, 2019-11-21]
2015 Stuff/3D Printed Parts - 2015/Stomach/BotBackLeftV1.stl
114.6 x 96.1 x 63.5
