TNTECHARC/TALUS-legacy/2015 Stuff/3D Printed Parts - 2015/Stomach/HipCoverFrontV1.stl

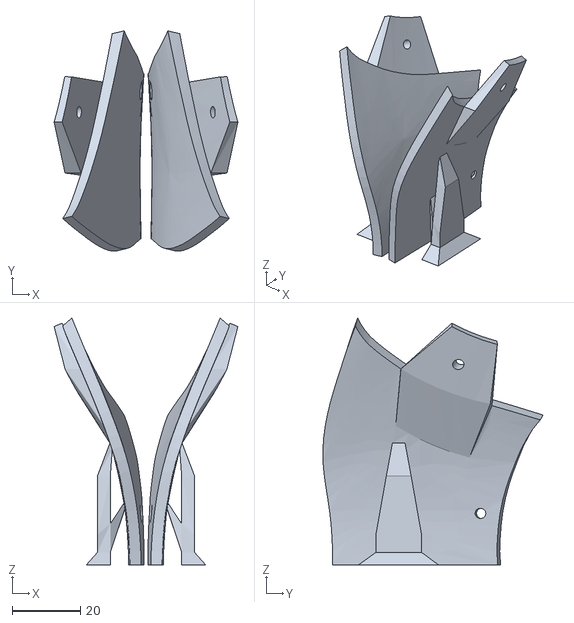
[picture p92: CAD file, 2019-11-21]
2015 Stuff/3D Printed Parts - 2015/Stomach/HipCoverFrontV1.stl
54.0 x 64.7 x 72.5
