TNTECHARC/TALUS-legacy/2015 Stuff/3D Printed Parts - 2015/Stomach/BotBackRigtV1.stl

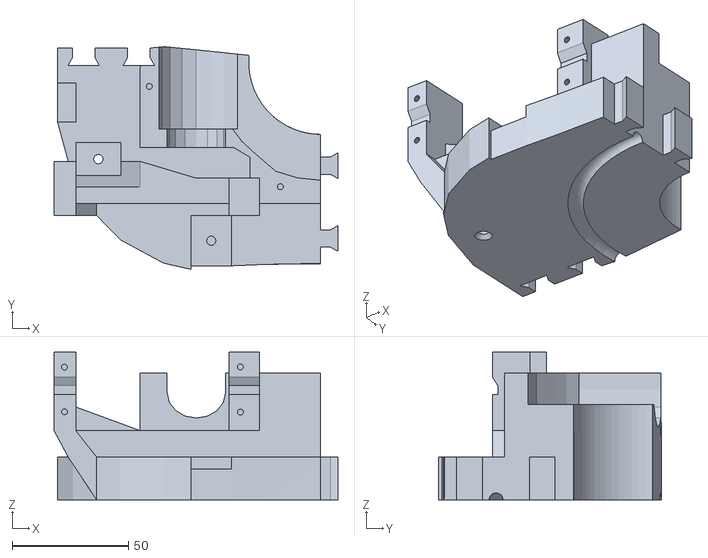
[picture p93: CAD file, 2019-11-21]
2015 Stuff/3D Printed Parts - 2015/Stomach/BotBackRigtV1.stl
122.0 x 95.7 x 63.5
