TNTECHARC/TALUS-legacy/2015 Stuff/3D Printed Parts - 2015/Stomach/StoGearAttachV1.stl

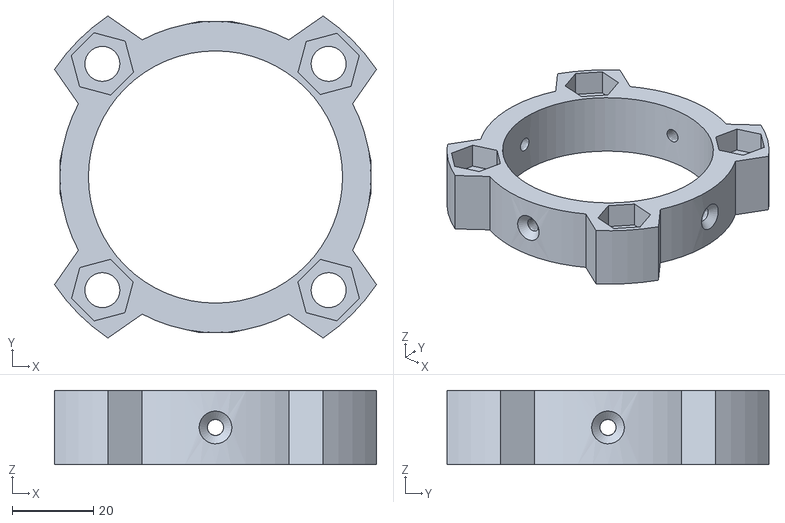
[picture p94: CAD file, 2019-11-21]
2015 Stuff/3D Printed Parts - 2015/Stomach/StoGearAttachV1.stl
79.1 x 79.1 x 18.2
