TNTECHARC/TALUS-legacy/2015 Stuff/3D Printed Parts - 2015/Stomach/RollBackRightV1.stl

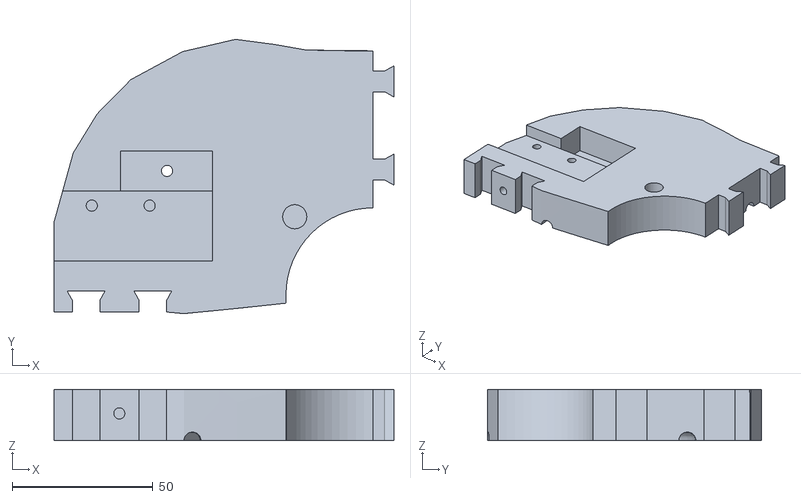
[picture p95: CAD file, 2019-11-21]
2015 Stuff/3D Printed Parts - 2015/Stomach/RollBackRightV1.stl
120.6 x 97.3 x 18.2
